skyhigh404/ESP32BiosignalMonitor/esp32/components/ad5941/include/ad5940.h

/**  
 * @file       ad5940.h
 * @brief      AD5940 library. This file contains all AD5940 library functions. 
 * @author     ADI
 * @date       March 2019
 * @par Revision History:
 * 
 * Copyright (c) 2017-2019 Analog Devices, Inc. All Rights Reserved.
 * 
 * This software is proprietary to Analog Devices, Inc. and its licensors.
 * By using this software you agree to the terms of the associated
 * Analog Devices Software License Agreement.
**/
#ifndef _AD5940_H_
#define _AD5940_H_
#include "math.h"
#include "string.h"
#include "stdio.h"
/** @addtogroup AD5940_Library
  * @{
  */

/** 
 * Select the correct chip.
 * Recommend to define this in your compiler.
 * */
//#define CHIPSEL_M355      /**< ADuCM355 */
//#define CHIPSEL_594X      /**< AD5940 or AD5941 */

/* library version number */
#define AD5940LIB_VER_MAJOR       0    /**< Major number */
#define AD5940LIB_VER_MINOR       2    /**< Minor number */
#define AD5940LIB_VER_PATCH       1    /**< Path number */
#define AD5940LIB_VER   (AD5940LIB_VER_MAJOR<<16)|(AD5940LIB_VER_MINOR<<8)|(AD5940LIB_VER_PATCH)

// #define ADI_DEBUG   /**< Comment this line to remove debug info. */

#ifdef ADI_DEBUG
#define ADI_Print printf   /**< Select the method to print out debug message */
#endif

#if defined(CHIPSEL_M355) && defined(CHIPSEL_594X)
#error Please select the correct chip by define CHIPSEL_M355 or CHIPSEL_594X.
#endif

#if !defined(CHIPSEL_M355) && !defined(CHIPSEL_594X)
#error Please select the correct chip by define CHIPSEL_M355 or CHIPSEL_594X.
#endif

/** 
 * @cond
 * @defgroup AD5940RegistersBitfields
 * @brief All AD5940 registers and bitfields definition.
 * @{
*/
//#if defined(_LANGUAGE_C) || (defined(__GNUC__) && !defined(__ASSEMBLER__))
#include <stdint.h>
//#endif /* _LANGUAGE_C */

#ifndef __ADI_GENERATED_DEF_HEADERS__
#define __ADI_GENERATED_DEF_HEADERS__    1
#endif

#define __ADI_HAS_AGPIO__          1
#define __ADI_HAS_ALLON__          1
#define __ADI_HAS_INTC__           1
#define __ADI_HAS_AFECON__         1
#define __ADI_HAS_WUPTMR__         1
#define __ADI_HAS_AFE__            1

/* ============================================================================================================================
        GPIO
   ============================================================================================================================ */

/* ============================================================================================================================
        AGPIO
   ============================================================================================================================ */
#define REG_AGPIO_GP0CON_RESET               0x00000000            /*      Reset Value for GP0CON  */
#define REG_AGPIO_GP0CON                     0x00000000            /*  AGPIO GPIO Port 0 Configuration */
#define REG_AGPIO_GP0OEN_RESET               0x00000000            /*      Reset Value for GP0OEN  */
#define REG_AGPIO_GP0OEN                     0x00000004            /*  AGPIO GPIO Port 0 Output Enable */
#define REG_AGPIO_GP0PE_RESET                0x00000000            /*      Reset Value for GP0PE  */
#define REG_AGPIO_GP0PE                      0x00000008            /*  AGPIO GPIO Port 0 Pullup/Pulldown Enable */
#define REG_AGPIO_GP0IEN_RESET               0x00000000            /*      Reset Value for GP0IEN  */
#define REG_AGPIO_GP0IEN                     0x0000000C            /*  AGPIO GPIO Port 0 Input Path Enable */
#define REG_AGPIO_GP0IN_RESET                0x00000000            /*      Reset Value for GP0IN  */
#define REG_AGPIO_GP0IN                      0x00000010            /*  AGPIO GPIO Port 0 Registered Data Input */
#define REG_AGPIO_GP0OUT_RESET               0x00000000            /*      Reset Value for GP0OUT  */
#define REG_AGPIO_GP0OUT                     0x00000014            /*  AGPIO GPIO Port 0 Data Output */
#define REG_AGPIO_GP0SET_RESET               0x00000000            /*      Reset Value for GP0SET  */
#define REG_AGPIO_GP0SET                     0x00000018            /*  AGPIO GPIO Port 0 Data Out Set */
#define REG_AGPIO_GP0CLR_RESET               0x00000000            /*      Reset Value for GP0CLR  */
#define REG_AGPIO_GP0CLR                     0x0000001C            /*  AGPIO GPIO Port 0 Data Out Clear */
#define REG_AGPIO_GP0TGL_RESET               0x00000000            /*      Reset Value for GP0TGL  */
#define REG_AGPIO_GP0TGL                     0x00000020            /*  AGPIO GPIO Port 0 Pin Toggle */

/* ============================================================================================================================
        AGPIO Register BitMasks, Positions & Enumerations 
   ============================================================================================================================ */
/* -------------------------------------------------------------------------------------------------------------------------
          AGPIO_GP0CON                         Pos/Masks         Description
   ------------------------------------------------------------------------------------------------------------------------- */
#define BITP_AGPIO_GP0CON_PIN7CFG            14            /*  P0.7 Configuration Bits */
#define BITP_AGPIO_GP0CON_PIN6CFG            12            /*  P0.6 Configuration Bits */
#define BITP_AGPIO_GP0CON_PIN5CFG            10            /*  P0.5 Configuration Bits */
#define BITP_AGPIO_GP0CON_PIN4CFG             8            /*  P0.4 Configuration Bits */
#define BITP_AGPIO_GP0CON_PIN3CFG             6            /*  P0.3 Configuration Bits */
#define BITP_AGPIO_GP0CON_PIN2CFG             4            /*  P0.2 Configuration Bits */
#define BITP_AGPIO_GP0CON_PIN1CFG             2            /*  P0.1 Configuration Bits */
#define BITP_AGPIO_GP0CON_PIN0CFG             0            /*  P0.0 Configuration Bits */
#define BITM_AGPIO_GP0CON_PIN7CFG            0x0000C000    /*  P0.7 Configuration Bits */
#define BITM_AGPIO_GP0CON_PIN6CFG            0x00003000    /*  P0.6 Configuration Bits */
#define BITM_AGPIO_GP0CON_PIN5CFG            0x00000C00    /*  P0.5 Configuration Bits */
#define BITM_AGPIO_GP0CON_PIN4CFG            0x00000300    /*  P0.4 Configuration Bits */
#define BITM_AGPIO_GP0CON_PIN3CFG            0x000000C0    /*  P0.3 Configuration Bits */
#define BITM_AGPIO_GP0CON_PIN2CFG            0x00000030    /*  P0.2 Configuration Bits */
#define BITM_AGPIO_GP0CON_PIN1CFG            0x0000000C    /*  P0.1 Configuration Bits */
#define BITM_AGPIO_GP0CON_PIN0CFG            0x00000003    /*  P0.0 Configuration Bits */

/* -------------------------------------------------------------------------------------------------------------------------
          AGPIO_GP0OEN                         Pos/Masks         Description
   ------------------------------------------------------------------------------------------------------------------------- */
#define BITP_AGPIO_GP0OEN_OEN                 0            /*  Pin Output Drive Enable */
#define BITM_AGPIO_GP0OEN_OEN                0x000000FF    /*  Pin Output Drive Enable */

/* -------------------------------------------------------------------------------------------------------------------------
          AGPIO_GP0PE                          Pos/Masks         Description
   ------------------------------------------------------------------------------------------------------------------------- */
#define BITP_AGPIO_GP0PE_PE                   0            /*  Pin Pull Enable */
#define BITM_AGPIO_GP0PE_PE                  0x000000FF    /*  Pin Pull Enable */

/* -------------------------------------------------------------------------------------------------------------------------
          AGPIO_GP0IEN                         Pos/Masks         Description
   ------------------------------------------------------------------------------------------------------------------------- */
#define BITP_AGPIO_GP0IEN_IEN                 0            /*  Input Path Enable */
#define BITM_AGPIO_GP0IEN_IEN                0x000000FF    /*  Input Path Enable */

/* -------------------------------------------------------------------------------------------------------------------------
          AGPIO_GP0IN                          Pos/Masks         Description
   ------------------------------------------------------------------------------------------------------------------------- */
#define BITP_AGPIO_GP0IN_IN                   0            /*  Registered Data Input */
#define BITM_AGPIO_GP0IN_IN                  0x000000FF    /*  Registered Data Input */

/* -------------------------------------------------------------------------------------------------------------------------
          AGPIO_GP0OUT                         Pos/Masks         Description
   ------------------------------------------------------------------------------------------------------------------------- */
#define BITP_AGPIO_GP0OUT_OUT                 0            /*  Data Out */
#define BITM_AGPIO_GP0OUT_OUT                0x000000FF    /*  Data Out */

/* -------------------------------------------------------------------------------------------------------------------------
          AGPIO_GP0SET                         Pos/Masks         Description
   ------------------------------------------------------------------------------------------------------------------------- */
#define BITP_AGPIO_GP0SET_SET                 0            /*  Set the Output HIGH */
#define BITM_AGPIO_GP0SET_SET                0x000000FF    /*  Set the Output HIGH */

/* -------------------------------------------------------------------------------------------------------------------------
          AGPIO_GP0CLR                         Pos/Masks         Description
   ------------------------------------------------------------------------------------------------------------------------- */
#define BITP_AGPIO_GP0CLR_CLR                 0            /*  Set the Output LOW */
#define BITM_AGPIO_GP0CLR_CLR                0x000000FF    /*  Set the Output LOW */

/* -------------------------------------------------------------------------------------------------------------------------
          AGPIO_GP0TGL                         Pos/Masks         Description
   ------------------------------------------------------------------------------------------------------------------------- */
#define BITP_AGPIO_GP0TGL_TGL                 0            /*  Toggle the Output */
#define BITM_AGPIO_GP0TGL_TGL                0x000000FF    /*  Toggle the Output */


/* ============================================================================================================================
        
   ============================================================================================================================ */

/* ============================================================================================================================
        AFECON
   ============================================================================================================================ */
#define REG_AFECON_ADIID_RESET               0x00000000            /*      Reset Value for ADIID  */
#define REG_AFECON_ADIID                     0x00000400            /*  AFECON ADI Identification */
#define REG_AFECON_CHIPID_RESET              0x00000000            /*      Reset Value for CHIPID  */
#define REG_AFECON_CHIPID                    0x00000404            /*  AFECON Chip Identification */
#define REG_AFECON_CLKCON0_RESET             0x00000441            /*      Reset Value for CLKCON0  */
#define REG_AFECON_CLKCON0                   0x00000408            /*  AFECON Clock Divider Configuration */
#define REG_AFECON_CLKEN1_RESET              0x000002C0            /*      Reset Value for CLKEN1  */
#define REG_AFECON_CLKEN1                    0x00000410            /*  AFECON Clock Gate Enable */
#define REG_AFECON_CLKSEL_RESET              0x00000000            /*      Reset Value for CLKSEL  */
#define REG_AFECON_CLKSEL                    0x00000414            /*  AFECON Clock Select */
#define REG_AFECON_CLKCON0KEY_RESET          0x00000000            /*      Reset Value for CLKCON0KEY  */
#define REG_AFECON_CLKCON0KEY                0x00000420            /*  AFECON Enable Clock Division to 8Mhz,4Mhz and 2Mhz */
#define REG_AFECON_SWRSTCON_RESET            0x00000001            /*      Reset Value for SWRSTCON  */
#define REG_AFECON_SWRSTCON                  0x00000424            /*  AFECON Software Reset */
#define REG_AFECON_TRIGSEQ_RESET             0x00000000            /*      Reset Value for TRIGSEQ  */
#define REG_AFECON_TRIGSEQ                   0x00000430            /*  AFECON Trigger Sequence */

/* ============================================================================================================================
        AFECON Register BitMasks, Positions & Enumerations 
   ============================================================================================================================ */
/* -------------------------------------------------------------------------------------------------------------------------
          AFECON_ADIID                         Pos/Masks         Description
   ------------------------------------------------------------------------------------------------------------------------- */
#define BITP_AFECON_ADIID_ADIID               0            /*  ADI Identifier. */
#define BITM_AFECON_ADIID_ADIID              0x0000FFFF    /*  ADI Identifier. */

/* -------------------------------------------------------------------------------------------------------------------------
          AFECON_CHIPID                        Pos/Masks         Description
   ------------------------------------------------------------------------------------------------------------------------- */
#define BITP_AFECON_CHIPID_PARTID             4            /*  Part Identifier */
#define BITP_AFECON_CHIPID_REVISION           0            /*  Silicon Revision Number */
#define BITM_AFECON_CHIPID_PARTID            0x0000FFF0    /*  Part Identifier */
#define BITM_AFECON_CHIPID_REVISION          0x0000000F    /*  Silicon Revision Number */

/* -------------------------------------------------------------------------------------------------------------------------
          AFECON_CLKCON0                       Pos/Masks         Description
   ------------------------------------------------------------------------------------------------------------------------- */
#define BITP_AFECON_CLKCON0_SFFTCLKDIVCNT    10            /*  SFFT Clock Divider Configuration */
#define BITP_AFECON_CLKCON0_ADCCLKDIV         6            /*  ADC Clock Divider Configuration */
#define BITP_AFECON_CLKCON0_SYSCLKDIV         0            /*  System Clock Divider Configuration */
#define BITM_AFECON_CLKCON0_SFFTCLKDIVCNT    0x0000FC00    /*  SFFT Clock Divider Configuration */
#define BITM_AFECON_CLKCON0_ADCCLKDIV        0x000003C0    /*  ADC Clock Divider Configuration */
#define BITM_AFECON_CLKCON0_SYSCLKDIV        0x0000003F    /*  System Clock Divider Configuration */

/* -------------------------------------------------------------------------------------------------------------------------
          AFECON_CLKEN1                        Pos/Masks         Description
   ------------------------------------------------------------------------------------------------------------------------- */
#define BITP_AFECON_CLKEN1_GPT1DIS            7            /*  GPT1 Clock Enable */
#define BITP_AFECON_CLKEN1_GPT0DIS            6            /*  GPT0 Clock Enable */
#define BITP_AFECON_CLKEN1_ACLKDIS            5            /*  ACLK Clock Enable */
#define BITM_AFECON_CLKEN1_GPT1DIS           0x00000080    /*  GPT1 Clock Enable */
#define BITM_AFECON_CLKEN1_GPT0DIS           0x00000040    /*  GPT0 Clock Enable */
#define BITM_AFECON_CLKEN1_ACLKDIS           0x00000020    /*  ACLK Clock Enable */

/* -------------------------------------------------------------------------------------------------------------------------
          AFECON_CLKSEL                        Pos/Masks         Description
   ------------------------------------------------------------------------------------------------------------------------- */
#define BITP_AFECON_CLKSEL_ADCCLKSEL          2            /*  Select ADC Clock Source */
#define BITP_AFECON_CLKSEL_SYSCLKSEL          0            /*  Select System Clock Source */
#define BITM_AFECON_CLKSEL_ADCCLKSEL         0x0000000C    /*  Select ADC Clock Source */
#define BITM_AFECON_CLKSEL_SYSCLKSEL         0x00000003    /*  Select System Clock Source */

/* -------------------------------------------------------------------------------------------------------------------------
          AFECON_CLKCON0KEY                    Pos/Masks         Description
   ------------------------------------------------------------------------------------------------------------------------- */
#define BITP_AFECON_CLKCON0KEY_DIVSYSCLK_ULP_EN  0            /*  Enable Clock Division to 8Mhz,4Mhz and 2Mhz */
#define BITM_AFECON_CLKCON0KEY_DIVSYSCLK_ULP_EN 0x0000FFFF    /*  Enable Clock Division to 8Mhz,4Mhz and 2Mhz */

/* -------------------------------------------------------------------------------------------------------------------------
          AFECON_SWRSTCON                      Pos/Masks         Description
   ------------------------------------------------------------------------------------------------------------------------- */
#define BITP_AFECON_SWRSTCON_SWRSTL           0            /*  Software Reset */
#define BITM_AFECON_SWRSTCON_SWRSTL          0x0000FFFF    /*  Software Reset */

/* -------------------------------------------------------------------------------------------------------------------------
          AFECON_TRIGSEQ                       Pos/Masks         Description
   ------------------------------------------------------------------------------------------------------------------------- */
#define BITP_AFECON_TRIGSEQ_TRIG3             3            /*  Trigger Sequence 3 */
#define BITP_AFECON_TRIGSEQ_TRIG2             2            /*  Trigger Sequence 2 */
#define BITP_AFECON_TRIGSEQ_TRIG1             1            /*  Trigger Sequence 1 */
#define BITP_AFECON_TRIGSEQ_TRIG0             0            /*  Trigger Sequence 0 */
#define BITM_AFECON_TRIGSEQ_TRIG3            0x00000008    /*  Trigger Sequence 3 */
#define BITM_AFECON_TRIGSEQ_TRIG2            0x00000004    /*  Trigger Sequence 2 */
#define BITM_AFECON_TRIGSEQ_TRIG1            0x00000002    /*  Trigger Sequence 1 */
#define BITM_AFECON_TRIGSEQ_TRIG0            0x00000001    /*  Trigger Sequence 0 */

/* ============================================================================================================================
        AFEWDT
   ============================================================================================================================ */
#define REG_AFEWDT_WDTLD                     0x00000900            /*  AFEWDT Watchdog Timer Load Value */
#define REG_AFEWDT_WDTVALS                   0x00000904            /*  AFEWDT Current Count Value */
#define REG_AFEWDT_WDTCON                    0x00000908            /*  AFEWDT Watchdog Timer Control Register */
#define REG_AFEWDT_WDTCLRI                   0x0000090C            /*  AFEWDT Refresh Watchdog Register */
#define REG_AFEWDT_WDTSTA                    0x00000918            /*  AFEWDT Timer Status */
#define REG_AFEWDT_WDTMINLD                  0x0000091C            /*  AFEWDT Minimum Load Value */

/* ============================================================================================================================
        AFEWDT Register BitMasks, Positions & Enumerations 
   ============================================================================================================================ */
/* -------------------------------------------------------------------------------------------------------------------------
          AFEWDT_WDTLD                         Pos/Masks         Description
   ------------------------------------------------------------------------------------------------------------------------- */
#define BITP_AFEWDT_WDTLD_LOAD                0            /*  WDT Load Value */
#define BITM_AFEWDT_WDTLD_LOAD               (_ADI_MSK_3(0x0000FFFF,0x0000FFFF, int16_t   ))    /*  WDT Load Value */

/* -------------------------------------------------------------------------------------------------------------------------
          AFEWDT_WDTVALS                       Pos/Masks         Description
   ------------------------------------------------------------------------------------------------------------------------- */
#define BITP_AFEWDT_WDTVALS_CCOUNT            0            /*  Current WDT Count Value. */
#define BITM_AFEWDT_WDTVALS_CCOUNT           (_ADI_MSK_3(0x0000FFFF,0x0000FFFF, int16_t   ))    /*  Current WDT Count Value. */

/* -------------------------------------------------------------------------------------------------------------------------
          AFEWDT_WDTCON                        Pos/Masks         Description
   ------------------------------------------------------------------------------------------------------------------------- */
#define BITP_AFEWDT_WDTCON_RESERVED_15_11    11            /*  RESERVED */
#define BITP_AFEWDT_WDTCON_WDTIRQEN          10            /*  WDT Interrupt Enable */
#define BITP_AFEWDT_WDTCON_MINLOAD_EN         9            /*  Timer Window Control */
#define BITP_AFEWDT_WDTCON_CLKDIV2            8            /*  Clock Source */
#define BITP_AFEWDT_WDTCON_RESERVED1_7        7            /*  Reserved */
#define BITP_AFEWDT_WDTCON_MDE                6            /*  Timer Mode Select */
#define BITP_AFEWDT_WDTCON_EN                 5            /*  Timer Enable */
#define BITP_AFEWDT_WDTCON_PRE                2            /*  Prescaler. */
#define BITP_AFEWDT_WDTCON_IRQ                1            /*  WDT Interrupt Enable */
#define BITP_AFEWDT_WDTCON_PDSTOP             0            /*  Power Down Stop Enable */
#define BITM_AFEWDT_WDTCON_RESERVED_15_11    (_ADI_MSK_3(0x0000F800,0x0000F800U, uint16_t  ))    /*  RESERVED */
#define BITM_AFEWDT_WDTCON_WDTIRQEN          (_ADI_MSK_3(0x00000400,0x00000400U, uint16_t  ))    /*  WDT Interrupt Enable */
#define BITM_AFEWDT_WDTCON_MINLOAD_EN        (_ADI_MSK_3(0x00000200,0x00000200U, uint16_t  ))    /*  Timer Window Control */
#define BITM_AFEWDT_WDTCON_CLKDIV2           (_ADI_MSK_3(0x00000100,0x00000100U, uint16_t  ))    /*  Clock Source */
#define BITM_AFEWDT_WDTCON_RESERVED1_7       (_ADI_MSK_3(0x00000080,0x00000080U, uint16_t  ))    /*  Reserved */
#define BITM_AFEWDT_WDTCON_MDE               (_ADI_MSK_3(0x00000040,0x00000040U, uint16_t  ))    /*  Timer Mode Select */
#define BITM_AFEWDT_WDTCON_EN                (_ADI_MSK_3(0x00000020,0x00000020U, uint16_t  ))    /*  Timer Enable */
#define BITM_AFEWDT_WDTCON_PRE               (_ADI_MSK_3(0x0000000C,0x0000000CU, uint16_t  ))    /*  Prescaler. */
#define BITM_AFEWDT_WDTCON_IRQ               (_ADI_MSK_3(0x00000002,0x00000002U, uint16_t  ))    /*  WDT Interrupt Enable */
#define BITM_AFEWDT_WDTCON_PDSTOP            (_ADI_MSK_3(0x00000001,0x00000001U, uint16_t  ))    /*  Power Down Stop Enable */
#define ENUM_AFEWDT_WDTCON_RESET             (_ADI_MSK_3(0x00000000,0x00000000U, uint16_t  ))    /*  IRQ: Watchdog Timer timeout creates a reset. */
#define ENUM_AFEWDT_WDTCON_INTERRUPT         (_ADI_MSK_3(0x00000002,0x00000002U, uint16_t  ))    /*  IRQ: Watchdog Timer  timeout creates an interrupt instead of reset. */
#define ENUM_AFEWDT_WDTCON_CONTINUE          (_ADI_MSK_3(0x00000000,0x00000000U, uint16_t  ))    /*  PDSTOP: Continue Counting When In Hibernate */
#define ENUM_AFEWDT_WDTCON_STOP              (_ADI_MSK_3(0x00000001,0x00000001U, uint16_t  ))    /*  PDSTOP: Stop Counter When In Hibernate. */

/* -------------------------------------------------------------------------------------------------------------------------
          AFEWDT_WDTCLRI                       Pos/Masks         Description
   ------------------------------------------------------------------------------------------------------------------------- */
#define BITP_AFEWDT_WDTCLRI_CLRWDG            0            /*  Refresh Register */
#define BITM_AFEWDT_WDTCLRI_CLRWDG           (_ADI_MSK_3(0x0000FFFF,0x0000FFFF, int16_t   ))    /*  Refresh Register */

/* -------------------------------------------------------------------------------------------------------------------------
          AFEWDT_WDTSTA                        Pos/Masks         Description
   ------------------------------------------------------------------------------------------------------------------------- */
#define BITP_AFEWDT_WDTSTA_RESERVED_15_7      7            /*  RESERVED */
#define BITP_AFEWDT_WDTSTA_TMINLD             6            /*  WDTMINLD Write Status */
#define BITP_AFEWDT_WDTSTA_OTPWRDONE          5            /*  Reset Type Status */
#define BITP_AFEWDT_WDTSTA_LOCK               4            /*  Lock Status */
#define BITP_AFEWDT_WDTSTA_CON                3            /*  WDTCON Write Status */
#define BITP_AFEWDT_WDTSTA_TLD                2            /*  WDTVAL Write Status */
#define BITP_AFEWDT_WDTSTA_CLRI               1            /*  WDTCLRI Write Status */
#define BITP_AFEWDT_WDTSTA_IRQ                0            /*  WDT Interrupt */
#define BITM_AFEWDT_WDTSTA_RESERVED_15_7     (_ADI_MSK_3(0x0000FF80,0x0000FF80U, uint16_t  ))    /*  RESERVED */
#define BITM_AFEWDT_WDTSTA_TMINLD            (_ADI_MSK_3(0x00000040,0x00000040U, uint16_t  ))    /*  WDTMINLD Write Status */
#define BITM_AFEWDT_WDTSTA_OTPWRDONE         (_ADI_MSK_3(0x00000020,0x00000020U, uint16_t  ))    /*  Reset Type Status */
#define BITM_AFEWDT_WDTSTA_LOCK              (_ADI_MSK_3(0x00000010,0x00000010U, uint16_t  ))    /*  Lock Status */
#define BITM_AFEWDT_WDTSTA_CON               (_ADI_MSK_3(0x00000008,0x00000008U, uint16_t  ))    /*  WDTCON Write Status */
#define BITM_AFEWDT_WDTSTA_TLD               (_ADI_MSK_3(0x00000004,0x00000004U, uint16_t  ))    /*  WDTVAL Write Status */
#define BITM_AFEWDT_WDTSTA_CLRI              (_ADI_MSK_3(0x00000002,0x00000002U, uint16_t  ))    /*  WDTCLRI Write Status */
#define BITM_AFEWDT_WDTSTA_IRQ               (_ADI_MSK_3(0x00000001,0x00000001U, uint16_t  ))    /*  WDT Interrupt */
#define ENUM_AFEWDT_WDTSTA_OPEN              (_ADI_MSK_3(0x00000000,0x00000000U, uint16_t  ))    /*  LOCK: Timer Operation Not Locked */
#define ENUM_AFEWDT_WDTSTA_LOCKED            (_ADI_MSK_3(0x00000010,0x00000010U, uint16_t  ))    /*  LOCK: Timer Enabled and Locked */
#define ENUM_AFEWDT_WDTSTA_SYNC_COMPLETE     (_ADI_MSK_3(0x00000000,0x00000000U, uint16_t  ))    /*  TLD: Arm and AFE Watchdog Clock Domains WDTLD values match */
#define ENUM_AFEWDT_WDTSTA_SYNC_IN_PROGRESS  (_ADI_MSK_3(0x00000004,0x00000004U, uint16_t  ))    /*  TLD: Synchronize In Progress */
#define ENUM_AFEWDT_WDTSTA_CLEARED           (_ADI_MSK_3(0x00000000,0x00000000U, uint16_t  ))    /*  IRQ: Watchdog Timer Interrupt Not Pending */
#define ENUM_AFEWDT_WDTSTA_PENDING           (_ADI_MSK_3(0x00000001,0x00000001U, uint16_t  ))    /*  IRQ: Watchdog Timer Interrupt Pending */

/* -------------------------------------------------------------------------------------------------------------------------
          AFEWDT_WDTMINLD                      Pos/Masks         Description
   ------------------------------------------------------------------------------------------------------------------------- */
#define BITP_AFEWDT_WDTMINLD_MIN_LOAD         0            /*  WDT Min Load Value */
#define BITM_AFEWDT_WDTMINLD_MIN_LOAD        (_ADI_MSK_3(0x0000FFFF,0x0000FFFF, int16_t   ))    /*  WDT Min Load Value */

/* ============================================================================================================================
        Wakeup Timer
   ============================================================================================================================ */

/* ============================================================================================================================
        WUPTMR
   ============================================================================================================================ */
#define REG_WUPTMR_CON_RESET                 0x00000000            /*      Reset Value for CON  */
#define REG_WUPTMR_CON                       0x00000800            /*  WUPTMR Timer Control */
#define REG_WUPTMR_SEQORDER_RESET            0x00000000            /*      Reset Value for SEQORDER  */
#define REG_WUPTMR_SEQORDER                  0x00000804            /*  WUPTMR Order Control */
#define REG_WUPTMR_SEQ0WUPL_RESET            0x0000FFFF            /*      Reset Value for SEQ0WUPL  */
#define REG_WUPTMR_SEQ0WUPL                  0x00000808            /*  WUPTMR SEQ0 WTimeL (LSB) */
#define REG_WUPTMR_SEQ0WUPH_RESET            0x0000000F            /*      Reset Value for SEQ0WUPH  */
#define REG_WUPTMR_SEQ0WUPH                  0x0000080C            /*  WUPTMR SEQ0 WTimeH (MSB) */
#define REG_WUPTMR_SEQ0SLEEPL_RESET          0x0000FFFF            /*      Reset Value for SEQ0SLEEPL  */
#define REG_WUPTMR_SEQ0SLEEPL                0x00000810            /*  WUPTMR SEQ0 STimeL (LSB) */
#define REG_WUPTMR_SEQ0SLEEPH_RESET          0x0000000F            /*      Reset Value for SEQ0SLEEPH  */
#define REG_WUPTMR_SEQ0SLEEPH                0x00000814            /*  WUPTMR SEQ0 STimeH (MSB) */
#define REG_WUPTMR_SEQ1WUPL_RESET            0x0000FFFF            /*      Reset Value for SEQ1WUPL  */
#define REG_WUPTMR_SEQ1WUPL                  0x00000818            /*  WUPTMR SEQ1 WTimeL (LSB) */
#define REG_WUPTMR_SEQ1WUPH_RESET            0x0000000F            /*      Reset Value for SEQ1WUPH  */
#define REG_WUPTMR_SEQ1WUPH                  0x0000081C            /*  WUPTMR SEQ1 WTimeH (MSB) */
#define REG_WUPTMR_SEQ1SLEEPL_RESET          0x0000FFFF            /*      Reset Value for SEQ1SLEEPL  */
#define REG_WUPTMR_SEQ1SLEEPL                0x00000820            /*  WUPTMR SEQ1 STimeL (LSB) */
#define REG_WUPTMR_SEQ1SLEEPH_RESET          0x0000000F            /*      Reset Value for SEQ1SLEEPH  */
#define REG_WUPTMR_SEQ1SLEEPH                0x00000824            /*  WUPTMR SEQ1 STimeH (MSB) */
#define REG_WUPTMR_SEQ2WUPL_RESET            0x0000FFFF            /*      Reset Value for SEQ2WUPL  */
#define REG_WUPTMR_SEQ2WUPL                  0x00000828            /*  WUPTMR SEQ2 WTimeL (LSB) */
#define REG_WUPTMR_SEQ2WUPH_RESET            0x0000000F            /*      Reset Value for SEQ2WUPH  */
#define REG_WUPTMR_SEQ2WUPH                  0x0000082C            /*  WUPTMR SEQ2 WTimeH (MSB) */
#define REG_WUPTMR_SEQ2SLEEPL_RESET          0x0000FFFF            /*      Reset Value for SEQ2SLEEPL  */
#define REG_WUPTMR_SEQ2SLEEPL                0x00000830            /*  WUPTMR SEQ2 STimeL (LSB) */
#define REG_WUPTMR_SEQ2SLEEPH_RESET          0x0000000F            /*      Reset Value for SEQ2SLEEPH  */
#define REG_WUPTMR_SEQ2SLEEPH                0x00000834            /*  WUPTMR SEQ2 STimeH (MSB) */
#define REG_WUPTMR_SEQ3WUPL_RESET            0x0000FFFF            /*      Reset Value for SEQ3WUPL  */
#define REG_WUPTMR_SEQ3WUPL                  0x00000838            /*  WUPTMR SEQ3 WTimeL (LSB) */
#define REG_WUPTMR_SEQ3WUPH_RESET            0x0000000F            /*      Reset Value for SEQ3WUPH  */
#define REG_WUPTMR_SEQ3WUPH                  0x0000083C            /*  WUPTMR SEQ3 WTimeH (MSB) */
#define REG_WUPTMR_SEQ3SLEEPL_RESET          0x0000FFFF            /*      Reset Value for SEQ3SLEEPL  */
#define REG_WUPTMR_SEQ3SLEEPL                0x00000840            /*  WUPTMR SEQ3 STimeL (LSB) */
#define REG_WUPTMR_SEQ3SLEEPH_RESET          0x0000000F            /*      Reset Value for SEQ3SLEEPH  */
#define REG_WUPTMR_SEQ3SLEEPH                0x00000844            /*  WUPTMR SEQ3 STimeH (MSB) */

/* ============================================================================================================================
        WUPTMR Register BitMasks, Positions & Enumerations 
   ============================================================================================================================ */
/* -------------------------------------------------------------------------------------------------------------------------
          WUPTMR_CON                           Pos/Masks         Description
   ------------------------------------------------------------------------------------------------------------------------- */
#define BITP_WUPTMR_CON_MSKTRG                6            /*  Mark Sequence Trigger from Sleep Wakeup Timer */
#define BITP_WUPTMR_CON_CLKSEL                4            /*  Clock Selection */
#define BITP_WUPTMR_CON_ENDSEQ                1            /*  End Sequence */
#define BITP_WUPTMR_CON_EN                    0            /*  Sleep Wake Timer Enable Bit */
#define BITM_WUPTMR_CON_MSKTRG               0x00000040    /*  Mark Sequence Trigger from Sleep Wakeup Timer */
#define BITM_WUPTMR_CON_CLKSEL               0x00000030    /*  Clock Selection */
#define BITM_WUPTMR_CON_ENDSEQ               0x0000000E    /*  End Sequence */
#define BITM_WUPTMR_CON_EN                   0x00000001    /*  Sleep Wake Timer Enable Bit */
#define ENUM_WUPTMR_CON_SWT32K0              0x00000000            /*  CLKSEL: Internal 32kHz OSC */
#define ENUM_WUPTMR_CON_SWTEXT0              0x00000010            /*  CLKSEL: External Clock */
#define ENUM_WUPTMR_CON_SWT32K               0x00000020            /*  CLKSEL: Internal 32kHz OSC */
#define ENUM_WUPTMR_CON_SWTEXT               0x00000030            /*  CLKSEL: External Clock */
#define ENUM_WUPTMR_CON_ENDSEQA              0x00000000            /*  ENDSEQ: The Sleep Wakeup Timer Will Stop At SeqA And Then Go Back To SeqA */
#define ENUM_WUPTMR_CON_ENDSEQB              0x00000002            /*  ENDSEQ: The Sleep Wakeup Timer Will Stop At SeqB And Then Go Back To SeqA */
#define ENUM_WUPTMR_CON_ENDSEQC              0x00000004            /*  ENDSEQ: The Sleep Wakeup Timer Will Stop At SeqC And Then Go Back To SeqA */
#define ENUM_WUPTMR_CON_ENDSEQD              0x00000006            /*  ENDSEQ: The Sleep Wakeup Timer Will Stop At SeqD And Then Go Back To SeqA */
#define ENUM_WUPTMR_CON_ENDSEQE              0x00000008            /*  ENDSEQ: The Sleep Wakeup Timer Will Stop At SeqE And Then Go Back To SeqA */
#define ENUM_WUPTMR_CON_ENDSEQF              0x0000000A            /*  ENDSEQ: The Sleep Wakeup Timer Will Stop At SeqF And Then Go Back To SeqA */
#define ENUM_WUPTMR_CON_ENDSEQG              0x0000000C            /*  ENDSEQ: The Sleep Wakeup Timer Will Stop At SeqG And Then Go Back To SeqA */
#define ENUM_WUPTMR_CON_ENDSEQH              0x0000000E            /*  ENDSEQ: The Sleep Wakeup Timer Will Stop At SeqH And Then Go Back To SeqA */
#define ENUM_WUPTMR_CON_SWTEN                0x00000000            /*  EN: Enable Sleep Wakeup Timer */
#define ENUM_WUPTMR_CON_SWTDIS               0x00000001            /*  EN: Disable Sleep Wakeup Timer */

/* -------------------------------------------------------------------------------------------------------------------------
          WUPTMR_SEQORDER                      Pos/Masks         Description
   ------------------------------------------------------------------------------------------------------------------------- */
#define BITP_WUPTMR_SEQORDER_SEQH            14            /*  SEQH Config */
#define BITP_WUPTMR_SEQORDER_SEQG            12            /*  SEQG Config */
#define BITP_WUPTMR_SEQORDER_SEQF            10            /*  SEQF Config */
#define BITP_WUPTMR_SEQORDER_SEQE             8            /*  SEQE Config */
#define BITP_WUPTMR_SEQORDER_SEQD             6            /*  SEQD Config */
#define BITP_WUPTMR_SEQORDER_SEQC             4            /*  SEQC Config */
#define BITP_WUPTMR_SEQORDER_SEQB             2            /*  SEQB Config */
#define BITP_WUPTMR_SEQORDER_SEQA             0            /*  SEQA Config */
#define BITM_WUPTMR_SEQORDER_SEQH            0x0000C000    /*  SEQH Config */
#define BITM_WUPTMR_SEQORDER_SEQG            0x00003000    /*  SEQG Config */
#define BITM_WUPTMR_SEQORDER_SEQF            0x00000C00    /*  SEQF Config */
#define BITM_WUPTMR_SEQORDER_SEQE            0x00000300    /*  SEQE Config */
#define BITM_WUPTMR_SEQORDER_SEQD            0x000000C0    /*  SEQD Config */
#define BITM_WUPTMR_SEQORDER_SEQC            0x00000030    /*  SEQC Config */
#define BITM_WUPTMR_SEQORDER_SEQB            0x0000000C    /*  SEQB Config */
#define BITM_WUPTMR_SEQORDER_SEQA            0x00000003    /*  SEQA Config */
#define ENUM_WUPTMR_SEQORDER_SEQH0           0x00000000            /*  SEQH: Fill SEQ0 In */
#define ENUM_WUPTMR_SEQORDER_SEQH1           0x00004000            /*  SEQH: Fill SEQ1 In */
#define ENUM_WUPTMR_SEQORDER_SEQH2           0x00008000            /*  SEQH: Fill SEQ2 In */
#define ENUM_WUPTMR_SEQORDER_SEQH3           0x0000C000            /*  SEQH: Fill SEQ3 In */
#define ENUM_WUPTMR_SEQORDER_SEQG0           0x00000000            /*  SEQG: Fill SEQ0 In */
#define ENUM_WUPTMR_SEQORDER_SEQG1           0x00001000            /*  SEQG: Fill SEQ1 In */
#define ENUM_WUPTMR_SEQORDER_SEQG2           0x00002000            /*  SEQG: Fill SEQ2 In */
#define ENUM_WUPTMR_SEQORDER_SEQG3           0x00003000            /*  SEQG: Fill SEQ3 In */
#define ENUM_WUPTMR_SEQORDER_SEQF0           0x00000000            /*  SEQF: Fill SEQ0 In */
#define ENUM_WUPTMR_SEQORDER_SEQF1           0x00000400            /*  SEQF: Fill SEQ1 In */
#define ENUM_WUPTMR_SEQORDER_SEQF2           0x00000800            /*  SEQF: Fill SEQ2 In */
#define ENUM_WUPTMR_SEQORDER_SEQF3           0x00000C00            /*  SEQF: Fill SEQ3 In */
#define ENUM_WUPTMR_SEQORDER_SEQE0           0x00000000            /*  SEQE: Fill SEQ0 In */
#define ENUM_WUPTMR_SEQORDER_SEQE1           0x00000100            /*  SEQE: Fill SEQ1 In */
#define ENUM_WUPTMR_SEQORDER_SEQE2           0x00000200            /*  SEQE: Fill SEQ2 In */
#define ENUM_WUPTMR_SEQORDER_SEQE3           0x00000300            /*  SEQE: Fill SEQ3 In */
#define ENUM_WUPTMR_SEQORDER_SEQD0           0x00000000            /*  SEQD: Fill SEQ0 In */
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
#define BITP_WUPTMR_SEQ3SLEEPL_SLEEPTIME3     0            /*  Sequence 3 Active Period */
#define BITM_WUPTMR_SEQ3SLEEPL_SLEEPTIME3    0x0000FFFF    /*  Sequence 3 Active Period */

/* -------------------------------------------------------------------------------------------------------------------------
          WUPTMR_SEQ3SLEEPH                    Pos/Masks         Description
   ------------------------------------------------------------------------------------------------------------------------- */
#define BITP_WUPTMR_SEQ3SLEEPH_SLEEPTIME3     0            /*  Sequence 3 Active Period */
#define BITM_WUPTMR_SEQ3SLEEPH_SLEEPTIME3    0x0000000F    /*  Sequence 3 Active Period */


/* ============================================================================================================================
        Always On Register
   ============================================================================================================================ */

/* ============================================================================================================================
        ALLON
   ============================================================================================================================ */
#define REG_ALLON_PWRMOD_RESET               0x00000001            /*      Reset Value for PWRMOD  */
#define REG_ALLON_PWRMOD                     0x00000A00            /*  ALLON Power Modes */
#define REG_ALLON_PWRKEY_RESET               0x00000000            /*      Reset Value for PWRKEY  */
#define REG_ALLON_PWRKEY                     0x00000A04            /*  ALLON Key Protection for PWRMOD */
#define REG_ALLON_OSCKEY_RESET               0x00000000            /*      Reset Value for OSCKEY  */
#define REG_ALLON_OSCKEY                     0x00000A0C            /*  ALLON Key Protection for OSCCON */
#define REG_ALLON_OSCCON_RESET               0x00000003            /*      Reset Value for OSCCON  */
#define REG_ALLON_OSCCON                     0x00000A10            /*  ALLON Oscillator Control */
#define REG_ALLON_TMRCON_RESET               0x00000000            /*      Reset Value for TMRCON  */
#define REG_ALLON_TMRCON                     0x00000A1C            /*  ALLON Timer Wakeup Configuration */
#define REG_ALLON_EI0CON_RESET               0x00000000            /*      Reset Value for EI0CON  */
#define REG_ALLON_EI0CON                     0x00000A20            /*  ALLON External Interrupt Configuration 0 */
#define REG_ALLON_EI1CON_RESET               0x00000000            /*      Reset Value for EI1CON  */
#define REG_ALLON_EI1CON                     0x00000A24            /*  ALLON External Interrupt Configuration 1 */
#define REG_ALLON_EI2CON_RESET               0x00000000            /*      Reset Value for EI2CON  */
#define REG_ALLON_EI2CON                     0x00000A28            /*  ALLON External Interrupt Configuration 2 */
#define REG_ALLON_EICLR_RESET                0x0000C000            /*      Reset Value for EICLR  */
#define REG_ALLON_EICLR                      0x00000A30            /*  ALLON External Interrupt Clear */
#define REG_ALLON_RSTSTA_RESET               0x00000000            /*      Reset Value for RSTSTA  */
#define REG_ALLON_RSTSTA                     0x00000A40            /*  ALLON Reset Status */
#define REG_ALLON_RSTCONKEY_RESET            0x00000000            /*      Reset Value for RSTCONKEY  */
#define REG_ALLON_RSTCONKEY                  0x00000A5C            /*  ALLON Key Protection for RSTCON Register */
#define REG_ALLON_LOSCTST_RESET              0x0000008F            /*      Reset Value for LOSCTST  */
#define REG_ALLON_LOSCTST                    0x00000A6C            /*  ALLON Internal LF Oscillator Test */
#define REG_ALLON_CLKEN0_RESET               0x00000004            /*      Reset Value for CLKEN0  */
#define REG_ALLON_CLKEN0                     0x00000A70            /*  ALLON 32KHz Peripheral Clock Enable */

/* ============================================================================================================================
        ALLON Register BitMasks, Positions & Enumerations 
   ============================================================================================================================ */
/* -------------------------------------------------------------------------------------------------------------------------
          ALLON_PWRMOD                         Pos/Masks         Description
   ------------------------------------------------------------------------------------------------------------------------- */
#define BITP_ALLON_PWRMOD_RAMRETEN           15            /*  Retention for RAM */
#define BITP_ALLON_PWRMOD_ADCRETEN           14            /*  Keep ADC Power Switch on in Hibernate */
#define BITP_ALLON_PWRMOD_SEQSLPEN            3            /*  Auto Sleep by Sequencer Command */
#define BITP_ALLON_PWRMOD_TMRSLPEN            2            /*  Auto Sleep by Sleep Wakeup Timer */
#define BITP_ALLON_PWRMOD_PWRMOD              0            /*  Power Mode Control Bits */
#define BITM_ALLON_PWRMOD_RAMRETEN           0x00008000    /*  Retention for RAM */
#define BITM_ALLON_PWRMOD_ADCRETEN           0x00004000    /*  Keep ADC Power Switch on in Hibernate */
#define BITM_ALLON_PWRMOD_SEQSLPEN           0x00000008    /*  Auto Sleep by Sequencer Command */
#define BITM_ALLON_PWRMOD_TMRSLPEN           0x00000004    /*  Auto Sleep by Sleep Wakeup Timer */
#define BITM_ALLON_PWRMOD_PWRMOD             0x00000003    /*  Power Mode Control Bits */

/* -------------------------------------------------------------------------------------------------------------------------
          ALLON_PWRKEY                         Pos/Masks         Description
   ------------------------------------------------------------------------------------------------------------------------- */
#define BITP_ALLON_PWRKEY_PWRKEY              0            /*  PWRMOD Key Register */
#define BITM_ALLON_PWRKEY_PWRKEY             0x0000FFFF    /*  PWRMOD Key Register */

/* -------------------------------------------------------------------------------------------------------------------------
          ALLON_OSCKEY                         Pos/Masks         Description
   ------------------------------------------------------------------------------------------------------------------------- */
#define BITP_ALLON_OSCKEY_OSCKEY              0            /*  Oscillator Control Key Register. */
#define BITM_ALLON_OSCKEY_OSCKEY             0x0000FFFF    /*  Oscillator Control Key Register. */

/* -------------------------------------------------------------------------------------------------------------------------
          ALLON_OSCCON                         Pos/Masks         Description
   ------------------------------------------------------------------------------------------------------------------------- */
#define BITP_ALLON_OSCCON_HFXTALOK           10            /*  Status of HFXTAL Oscillator */
#define BITP_ALLON_OSCCON_HFOSCOK             9            /*  Status of HFOSC Oscillator */
#define BITP_ALLON_OSCCON_LFOSCOK             8            /*  Status of LFOSC Oscillator */
#define BITP_ALLON_OSCCON_HFXTALEN            2            /*  High Frequency Crystal Oscillator Enable */
#define BITP_ALLON_OSCCON_HFOSCEN             1            /*  High Frequency Internal Oscillator Enable */
#define BITP_ALLON_OSCCON_LFOSCEN             0            /*  Low Frequency Internal Oscillator Enable */
#define BITM_ALLON_OSCCON_HFXTALOK           0x00000400    /*  Status of HFXTAL Oscillator */
#define BITM_ALLON_OSCCON_HFOSCOK            0x00000200    /*  Status of HFOSC Oscillator */
#define BITM_ALLON_OSCCON_LFOSCOK            0x00000100    /*  Status of LFOSC Oscillator */
#define BITM_ALLON_OSCCON_HFXTALEN           0x00000004    /*  High Frequency Crystal Oscillator Enable */
#define BITM_ALLON_OSCCON_HFOSCEN            0x00000002    /*  High Frequency Internal Oscillator Enable */
#define BITM_ALLON_OSCCON_LFOSCEN            0x00000001    /*  Low Frequency Internal Oscillator Enable */

/* -------------------------------------------------------------------------------------------------------------------------
          ALLON_TMRCON                         Pos/Masks         Description
   ------------------------------------------------------------------------------------------------------------------------- */
#define BITP_ALLON_TMRCON_TMRINTEN            0            /*  Enable Wakeup Timer */
#define BITM_ALLON_TMRCON_TMRINTEN           0x00000001    /*  Enable Wakeup Timer */

/* -------------------------------------------------------------------------------------------------------------------------
          ALLON_EI0CON                         Pos/Masks         Description
   ------------------------------------------------------------------------------------------------------------------------- */
#define BITP_ALLON_EI0CON_IRQ3EN             15            /*  External Interrupt 3 Enable Bit */
#define BITP_ALLON_EI0CON_IRQ3MDE            12            /*  External Interrupt 3 Mode Registers */
#define BITP_ALLON_EI0CON_IRQ2EN             11            /*  External Interrupt 2 Enable Bit */
#define BITP_ALLON_EI0CON_IRQ2MDE             8            /*  External Interrupt 2 Mode Registers */
#define BITP_ALLON_EI0CON_IRQ1EN              7            /*  External Interrupt 1 Enable Bit */
#define BITP_ALLON_EI0CON_IRQ1MDE             4            /*  External Interrupt 1 Mode Registers */
#define BITP_ALLON_EI0CON_IRQ0EN              3            /*  External Interrupt 0 Enable Bit */
#define BITP_ALLON_EI0CON_IRQ0MDE             0            /*  External Interrupt 0 Mode Registers */
#define BITM_ALLON_EI0CON_IRQ3EN             0x00008000    /*  External Interrupt 3 Enable Bit */
#define BITM_ALLON_EI0CON_IRQ3MDE            0x00007000    /*  External Interrupt 3 Mode Registers */
#define BITM_ALLON_EI0CON_IRQ2EN             0x00000800    /*  External Interrupt 2 Enable Bit */
#define BITM_ALLON_EI0CON_IRQ2MDE            0x00000700    /*  External Interrupt 2 Mode Registers */
#define BITM_ALLON_EI0CON_IRQ1EN             0x00000080    /*  External Interrupt 1 Enable Bit */
#define BITM_ALLON_EI0CON_IRQ1MDE            0x00000070    /*  External Interrupt 1 Mode Registers */
#define BITM_ALLON_EI0CON_IRQ0EN             0x00000008    /*  External Interrupt 0 Enable Bit */
#define BITM_ALLON_EI0CON_IRQ0MDE            0x00000007    /*  External Interrupt 0 Mode Registers */

/* -------------------------------------------------------------------------------------------------------------------------
          ALLON_EI1CON                         Pos/Masks         Description
   ------------------------------------------------------------------------------------------------------------------------- */
#define BITP_ALLON_EI1CON_IRQ7EN             15            /*  External Interrupt 7 Enable Bit */
#define BITP_ALLON_EI1CON_IRQ7MDE            12            /*  External Interrupt 7 Mode Registers */
#define BITP_ALLON_EI1CON_IRQ6EN             11            /*  External Interrupt 6 Enable Bit */
#define BITP_ALLON_EI1CON_IRQ6MDE             8            /*  External Interrupt 6 Mode Registers */
#define BITP_ALLON_EI1CON_IRQ5EN              7            /*  External Interrupt 5 Enable Bit */
#define BITP_ALLON_EI1CON_IRQ5MDE             4            /*  External Interrupt 5 Mode Registers */
#define BITP_ALLON_EI1CON_IRQ4EN              3            /*  External Interrupt 4 Enable Bit */
#define BITP_ALLON_EI1CON_IRQ4MDE             0            /*  External Interrupt 4 Mode Registers */
#define BITM_ALLON_EI1CON_IRQ7EN             0x00008000    /*  External Interrupt 7 Enable Bit */
#define BITM_ALLON_EI1CON_IRQ7MDE            0x00007000    /*  External Interrupt 7 Mode Registers */
#define BITM_ALLON_EI1CON_IRQ6EN             0x00000800    /*  External Interrupt 6 Enable Bit */
#define BITM_ALLON_EI1CON_IRQ6MDE            0x00000700    /*  External Interrupt 6 Mode Registers */
#define BITM_ALLON_EI1CON_IRQ5EN             0x00000080    /*  External Interrupt 5 Enable Bit */
#define BITM_ALLON_EI1CON_IRQ5MDE            0x00000070    /*  External Interrupt 5 Mode Registers */
#define BITM_ALLON_EI1CON_IRQ4EN             0x00000008    /*  External Interrupt 4 Enable Bit */
#define BITM_ALLON_EI1CON_IRQ4MDE            0x00000007    /*  External Interrupt 4 Mode Registers */

/* -------------------------------------------------------------------------------------------------------------------------
          ALLON_EI2CON                         Pos/Masks         Description
   ------------------------------------------------------------------------------------------------------------------------- */
#define BITP_ALLON_EI2CON_BUSINTEN            3            /*  BUS Interrupt Detection Enable Bit */
#define BITP_ALLON_EI2CON_BUSINTMDE           0            /*  BUS Interrupt Detection Mode Registers */
#define BITM_ALLON_EI2CON_BUSINTEN           0x00000008    /*  BUS Interrupt Detection Enable Bit */
#define BITM_ALLON_EI2CON_BUSINTMDE          0x00000007    /*  BUS Interrupt Detection Mode Registers */

/* -------------------------------------------------------------------------------------------------------------------------
          ALLON_EICLR                          Pos/Masks         Description
   ------------------------------------------------------------------------------------------------------------------------- */
#define BITP_ALLON_EICLR_AUTCLRBUSEN         15            /*  Enable Auto Clear of Bus Interrupt */
#define BITP_ALLON_EICLR_BUSINT               8            /*  BUS Interrupt */
#define BITM_ALLON_EICLR_AUTCLRBUSEN         0x00008000    /*  Enable Auto Clear of Bus Interrupt */
#define BITM_ALLON_EICLR_BUSINT              0x00000100    /*  BUS Interrupt */

/* -------------------------------------------------------------------------------------------------------------------------
          ALLON_RSTSTA                         Pos/Masks         Description
   ------------------------------------------------------------------------------------------------------------------------- */
#define BITP_ALLON_RSTSTA_PINSWRST            4            /*  Software Reset Pin */
#define BITP_ALLON_RSTSTA_MMRSWRST            3            /*  MMR Software Reset */
#define BITP_ALLON_RSTSTA_WDRST               2            /*  Watchdog Timeout */
#define BITP_ALLON_RSTSTA_EXTRST              1            /*  External Reset */
#define BITP_ALLON_RSTSTA_POR                 0            /*  Power-on Reset */
#define BITM_ALLON_RSTSTA_PINSWRST           0x00000010    /*  Software Reset Pin */
#define BITM_ALLON_RSTSTA_MMRSWRST           0x00000008    /*  MMR Software Reset */
#define BITM_ALLON_RSTSTA_WDRST              0x00000004    /*  Watchdog Timeout */
#define BITM_ALLON_RSTSTA_EXTRST             0x00000002    /*  External Reset */
#define BITM_ALLON_RSTSTA_POR                0x00000001    /*  Power-on Reset */

/* -------------------------------------------------------------------------------------------------------------------------
          ALLON_RSTCONKEY                      Pos/Masks         Description
   ------------------------------------------------------------------------------------------------------------------------- */
#define BITP_ALLON_RSTCONKEY_KEY              0            /*  Reset Control Key Register */
#define BITM_ALLON_RSTCONKEY_KEY             0x0000FFFF    /*  Reset Control Key Register */

/* -------------------------------------------------------------------------------------------------------------------------
          ALLON_LOSCTST                        Pos/Masks         Description
   ------------------------------------------------------------------------------------------------------------------------- */
#define BITP_ALLON_LOSCTST_TRIM               0            /*  Trim Caps to Adjust Frequency. */
#define BITM_ALLON_LOSCTST_TRIM              0x0000000F    /*  Trim Caps to Adjust Frequency. */

/* -------------------------------------------------------------------------------------------------------------------------
          ALLON_CLKEN0                         Pos/Masks         Description
   ------------------------------------------------------------------------------------------------------------------------- */
#define BITP_ALLON_CLKEN0_TIACHPDIS           2            /*  TIA Chop Clock Disable */
#define BITP_ALLON_CLKEN0_SLPWUTDIS           1            /*  Sleep/Wakeup Timer Clock Disable */
#define BITP_ALLON_CLKEN0_WDTDIS              0            /*  Watch Dog Timer Clock Disable */
#define BITM_ALLON_CLKEN0_TIACHPDIS          0x00000004    /*  TIA Chop Clock Disable */
#define BITM_ALLON_CLKEN0_SLPWUTDIS          0x00000002    /*  Sleep/Wakeup Timer Clock Disable */
#define BITM_ALLON_CLKEN0_WDTDIS             0x00000001    /*  Watch Dog Timer Clock Disable */

/* ============================================================================================================================
        General Purpose Timer
   ============================================================================================================================ */

/* ============================================================================================================================
        AGPT0
   ============================================================================================================================ */
#define REG_AGPT0_LD0                        0x00000D00            /*  AGPT0 16-bit Load Value Register. */
#define REG_AGPT0_VAL0                       0x00000D04            /*  AGPT0 16-Bit Timer Value Register. */
#define REG_AGPT0_CON0                       0x00000D08            /*  AGPT0 Control Register. */
#define REG_AGPT0_CLRI0                      0x00000D0C            /*  AGPT0 Clear Interrupt Register. */
#define REG_AGPT0_CAP0                       0x00000D10            /*  AGPT0 Capture Register. */
#define REG_AGPT0_ALD0                       0x00000D14            /*  AGPT0 16-Bit Load Value, Asynchronous. */
#define REG_AGPT0_AVAL0                      0x00000D18            /*  AGPT0 16-Bit Timer Value, Asynchronous Register. */
#define REG_AGPT0_STA0                       0x00000D1C            /*  AGPT0 Status Register. */
#define REG_AGPT0_PWMCON0                    0x00000D20            /*  AGPT0 PWM Control Register. */
#define REG_AGPT0_PWMMAT0                    0x00000D24            /*  AGPT0 PWM Match Value Register. */
#define REG_AGPT0_INTEN                      0x00000D28            /*  AGPT0 Interrupt Enable */

/* ============================================================================================================================
        AGPT0 Register BitMasks, Positions & Enumerations 
   ============================================================================================================================ */
/* -------------------------------------------------------------------------------------------------------------------------
          AGPT0_LD0                            Pos/Masks         Description
   ------------------------------------------------------------------------------------------------------------------------- */
#define BITP_AGPT0_LD0_LOAD                   0            /*  Load Value */
#define BITM_AGPT0_LD0_LOAD                  (_ADI_MSK_3(0x0000FFFF,0x0000FFFF, int16_t   ))    /*  Load Value */

/* -------------------------------------------------------------------------------------------------------------------------
          AGPT0_VAL0                           Pos/Masks         Description
   ------------------------------------------------------------------------------------------------------------------------- */
#define BITP_AGPT0_VAL0_VAL                   0            /*  Current Count */
#define BITM_AGPT0_VAL0_VAL                  (_ADI_MSK_3(0x0000FFFF,0x0000FFFF, int16_t   ))    /*  Current Count */

/* -------------------------------------------------------------------------------------------------------------------------
          AGPT0_CON0                           Pos/Masks         Description
   ------------------------------------------------------------------------------------------------------------------------- */
#define BITP_AGPT0_CON0_SYNCBYP              15            /*  Synchronization Bypass */
#define BITP_AGPT0_CON0_RSTEN                14            /*  Counter and Prescale Reset Enable */
#define BITP_AGPT0_CON0_EVTEN                13            /*  Event Select */
#define BITP_AGPT0_CON0_EVENT                 8            /*  Event Select Range */
#define BITP_AGPT0_CON0_RLD                   7            /*  Reload Control */
#define BITP_AGPT0_CON0_CLK                   5            /*  Clock Select */
#define BITP_AGPT0_CON0_ENABLE                4            /*  Timer Enable */
#define BITP_AGPT0_CON0_MOD                   3            /*  Timer Mode */
#define BITP_AGPT0_CON0_UP                    2            /*  Count up */
#define BITP_AGPT0_CON0_PRE                   0            /*  Prescaler */
#define BITM_AGPT0_CON0_SYNCBYP              (_ADI_MSK_3(0x00008000,0x00008000U, uint16_t  ))    /*  Synchronization Bypass */
#define BITM_AGPT0_CON0_RSTEN                (_ADI_MSK_3(0x00004000,0x00004000U, uint16_t  ))    /*  Counter and Prescale Reset Enable */
#define BITM_AGPT0_CON0_EVTEN                (_ADI_MSK_3(0x00002000,0x00002000U, uint16_t  ))    /*  Event Select */
#define BITM_AGPT0_CON0_EVENT                (_ADI_MSK_3(0x00001F00,0x00001F00U, uint16_t  ))    /*  Event Select Range */
#define BITM_AGPT0_CON0_RLD                  (_ADI_MSK_3(0x00000080,0x00000080U, uint16_t  ))    /*  Reload Control */
#define BITM_AGPT0_CON0_CLK                  (_ADI_MSK_3(0x00000060,0x00000060U, uint16_t  ))    /*  Clock Select */
#define BITM_AGPT0_CON0_ENABLE               (_ADI_MSK_3(0x00000010,0x00000010U, uint16_t  ))    /*  Timer Enable */
#define BITM_AGPT0_CON0_MOD                  (_ADI_MSK_3(0x00000008,0x00000008U, uint16_t  ))    /*  Timer Mode */
#define BITM_AGPT0_CON0_UP                   (_ADI_MSK_3(0x00000004,0x00000004U, uint16_t  ))    /*  Count up */
#define BITM_AGPT0_CON0_PRE                  (_ADI_MSK_3(0x00000003,0x00000003U, uint16_t  ))    /*  Prescaler */

/* -------------------------------------------------------------------------------------------------------------------------
          AGPT0_CLRI0                          Pos/Masks         Description
   ------------------------------------------------------------------------------------------------------------------------- */
#define BITP_AGPT0_CLRI0_CAP                  1            /*  Clear Captured Event Interrupt */
#define BITP_AGPT0_CLRI0_TMOUT                0            /*  Clear Timeout Interrupt */
#define BITM_AGPT0_CLRI0_CAP                 (_ADI_MSK_3(0x00000002,0x00000002U, uint16_t  ))    /*  Clear Captured Event Interrupt */
#define BITM_AGPT0_CLRI0_TMOUT               (_ADI_MSK_3(0x00000001,0x00000001U, uint16_t  ))    /*  Clear Timeout Interrupt */

/* -------------------------------------------------------------------------------------------------------------------------
          AGPT0_CAP0                           Pos/Masks         Description
   ------------------------------------------------------------------------------------------------------------------------- */
#define BITP_AGPT0_CAP0_CAP                   0            /*  16-bit Captured Value */
#define BITM_AGPT0_CAP0_CAP                  (_ADI_MSK_3(0x0000FFFF,0x0000FFFF, int16_t   ))    /*  16-bit Captured Value */

/* -------------------------------------------------------------------------------------------------------------------------
          AGPT0_ALD0                           Pos/Masks         Description
   ------------------------------------------------------------------------------------------------------------------------- */
#define BITP_AGPT0_ALD0_ALOAD                 0            /*  Load Value, Asynchronous */
#define BITM_AGPT0_ALD0_ALOAD                (_ADI_MSK_3(0x0000FFFF,0x0000FFFF, int16_t   ))    /*  Load Value, Asynchronous */

/* -------------------------------------------------------------------------------------------------------------------------
          AGPT0_AVAL0                          Pos/Masks         Description
   ------------------------------------------------------------------------------------------------------------------------- */
#define BITP_AGPT0_AVAL0_AVAL                 0            /*  Counter Value */
#define BITM_AGPT0_AVAL0_AVAL                (_ADI_MSK_3(0x0000FFFF,0x0000FFFF, int16_t   ))    /*  Counter Value */

/* -------------------------------------------------------------------------------------------------------------------------
          AGPT0_STA0                           Pos/Masks         Description
   ------------------------------------------------------------------------------------------------------------------------- */
#define BITP_AGPT0_STA0_RSTCNT                8            /*  Counter Reset Occurring */
#define BITP_AGPT0_STA0_PDOK                  7            /*  Clear Interrupt Register Synchronization */
#define BITP_AGPT0_STA0_BUSY                  6            /*  Timer Busy */
#define BITP_AGPT0_STA0_CAP                   1            /*  Capture Event Pending */
#define BITP_AGPT0_STA0_TMOUT                 0            /*  Timeout Event Occurred */
#define BITM_AGPT0_STA0_RSTCNT               (_ADI_MSK_3(0x00000100,0x00000100U, uint16_t  ))    /*  Counter Reset Occurring */
#define BITM_AGPT0_STA0_PDOK                 (_ADI_MSK_3(0x00000080,0x00000080U, uint16_t  ))    /*  Clear Interrupt Register Synchronization */
#define BITM_AGPT0_STA0_BUSY                 (_ADI_MSK_3(0x00000040,0x00000040U, uint16_t  ))    /*  Timer Busy */
#define BITM_AGPT0_STA0_CAP                  (_ADI_MSK_3(0x00000002,0x00000002U, uint16_t  ))    /*  Capture Event Pending */
#define BITM_AGPT0_STA0_TMOUT                (_ADI_MSK_3(0x00000001,0x00000001U, uint16_t  ))    /*  Timeout Event Occurred */

/* -------------------------------------------------------------------------------------------------------------------------
          AGPT0_PWMCON0                        Pos/Masks         Description
   ------------------------------------------------------------------------------------------------------------------------- */
#define BITP_AGPT0_PWMCON0_IDLE               1            /*  PWM Idle State */
#define BITP_AGPT0_PWMCON0_MATCHEN            0            /*  PWM Match Enabled */
#define BITM_AGPT0_PWMCON0_IDLE              (_ADI_MSK_3(0x00000002,0x00000002U, uint16_t  ))    /*  PWM Idle State */
#define BITM_AGPT0_PWMCON0_MATCHEN           (_ADI_MSK_3(0x00000001,0x00000001U, uint16_t  ))    /*  PWM Match Enabled */

/* -------------------------------------------------------------------------------------------------------------------------
          AGPT0_PWMMAT0                        Pos/Masks         Description
   ------------------------------------------------------------------------------------------------------------------------- */
#define BITP_AGPT0_PWMMAT0_MATCHVAL           0            /*  PWM Match Value */
#define BITM_AGPT0_PWMMAT0_MATCHVAL          (_ADI_MSK_3(0x0000FFFF,0x0000FFFF, int16_t   ))    /*  PWM Match Value */

/* -------------------------------------------------------------------------------------------------------------------------
          AGPT0_INTEN                          Pos/Masks         Description
   ------------------------------------------------------------------------------------------------------------------------- */
#define BITP_AGPT0_INTEN_INTEN                0            /*  Interrupt Enable */
#define BITM_AGPT0_INTEN_INTEN               (_ADI_MSK_3(0x00000001,0x00000001U, uint16_t  ))    /*  Interrupt Enable */


/* ============================================================================================================================
        General Purpose Timer
   ============================================================================================================================ */

/* ============================================================================================================================
        AGPT1
   ============================================================================================================================ */
#define REG_AGPT1_LD1                        0x00000E00            /*  AGPT1 16-bit Load Value Register */
#define REG_AGPT1_VAL1                       0x00000E04            /*  AGPT1 16-bit Timer Value Register */
#define REG_AGPT1_CON1                       0x00000E08            /*  AGPT1 Control Register */
#define REG_AGPT1_CLRI1                      0x00000E0C            /*  AGPT1 Clear Interrupt Register */
#define REG_AGPT1_CAP1                       0x00000E10            /*  AGPT1 Capture Register */
#define REG_AGPT1_ALD1                       0x00000E14            /*  AGPT1 16-bit Load Value, Asynchronous Register */
#define REG_AGPT1_AVAL1                      0x00000E18            /*  AGPT1 16-bit Timer Value, Asynchronous Register */
#define REG_AGPT1_STA1                       0x00000E1C            /*  AGPT1 Status Register */
#define REG_AGPT1_PWMCON1                    0x00000E20            /*  AGPT1 PWM Control Register */
#define REG_AGPT1_PWMMAT1                    0x00000E24            /*  AGPT1 PWM Match Value Register */
#define REG_AGPT1_INTEN1                     0x00000E28            /*  AGPT1 Interrupt Enable */

/* ============================================================================================================================
        AGPT1 Register BitMasks, Positions & Enumerations 
   ============================================================================================================================ */
/* -------------------------------------------------------------------------------------------------------------------------
          AGPT1_LD1                            Pos/Masks         Description
   ------------------------------------------------------------------------------------------------------------------------- */
#define BITP_AGPT1_LD1_LOAD                   0            /*  Load Value */
#define BITM_AGPT1_LD1_LOAD                  (_ADI_MSK_3(0x0000FFFF,0x0000FFFF, int16_t   ))    /*  Load Value */

/* -------------------------------------------------------------------------------------------------------------------------
          AGPT1_VAL1                           Pos/Masks         Description
   ------------------------------------------------------------------------------------------------------------------------- */
#define BITP_AGPT1_VAL1_VAL                   0            /*  Current Count */
#define BITM_AGPT1_VAL1_VAL                  (_ADI_MSK_3(0x0000FFFF,0x0000FFFF, int16_t   ))    /*  Current Count */

/* -------------------------------------------------------------------------------------------------------------------------
          AGPT1_CON1                           Pos/Masks         Description
   ------------------------------------------------------------------------------------------------------------------------- */
#define BITP_AGPT1_CON1_SYNCBYP              15            /*  Synchronization Bypass */
#define BITP_AGPT1_CON1_RSTEN                14            /*  Counter and Prescale Reset Enable */
#define BITP_AGPT1_CON1_EVENTEN              13            /*  Event Select */
#define BITP_AGPT1_CON1_EVENT                 8            /*  Event Select Range */
#define BITP_AGPT1_CON1_RLD                   7            /*  Reload Control */
#define BITP_AGPT1_CON1_CLK                   5            /*  Clock Select */
#define BITP_AGPT1_CON1_ENABLE                4            /*  Timer Enable */
#define BITP_AGPT1_CON1_MOD                   3            /*  Timer Mode */
#define BITP_AGPT1_CON1_UP                    2            /*  Count up */
#define BITP_AGPT1_CON1_PRE                   0            /*  Prescaler */
#define BITM_AGPT1_CON1_SYNCBYP              (_ADI_MSK_3(0x00008000,0x00008000U, uint16_t  ))    /*  Synchronization Bypass */
#define BITM_AGPT1_CON1_RSTEN                (_ADI_MSK_3(0x00004000,0x00004000U, uint16_t  ))    /*  Counter and Prescale Reset Enable */
#define BITM_AGPT1_CON1_EVENTEN              (_ADI_MSK_3(0x00002000,0x00002000U, uint16_t  ))    /*  Event Select */
#define BITM_AGPT1_CON1_EVENT                (_ADI_MSK_3(0x00001F00,0x00001F00U, uint16_t  ))    /*  Event Select Range */
#define BITM_AGPT1_CON1_RLD                  (_ADI_MSK_3(0x00000080,0x00000080U, uint16_t  ))    /*  Reload Control */
#define BITM_AGPT1_CON1_CLK                  (_ADI_MSK_3(0x00000060,0x00000060U, uint16_t  ))    /*  Clock Select */
#define BITM_AGPT1_CON1_ENABLE               (_ADI_MSK_3(0x00000010,0x00000010U, uint16_t  ))    /*  Timer Enable */
#define BITM_AGPT1_CON1_MOD                  (_ADI_MSK_3(0x00000008,0x00000008U, uint16_t  ))    /*  Timer Mode */
#define BITM_AGPT1_CON1_UP                   (_ADI_MSK_3(0x00000004,0x00000004U, uint16_t  ))    /*  Count up */
#define BITM_AGPT1_CON1_PRE                  (_ADI_MSK_3(0x00000003,0x00000003U, uint16_t  ))    /*  Prescaler */

/* -------------------------------------------------------------------------------------------------------------------------
          AGPT1_CLRI1                          Pos/Masks         Description
   ------------------------------------------------------------------------------------------------------------------------- */
#define BITP_AGPT1_CLRI1_CAP                  1            /*  Clear Captured Event Interrupt */
#define BITP_AGPT1_CLRI1_TMOUT                0            /*  Clear Timeout Interrupt */
#define BITM_AGPT1_CLRI1_CAP                 (_ADI_MSK_3(0x00000002,0x00000002U, uint16_t  ))    /*  Clear Captured Event Interrupt */
#define BITM_AGPT1_CLRI1_TMOUT               (_ADI_MSK_3(0x00000001,0x00000001U, uint16_t  ))    /*  Clear Timeout Interrupt */

/* -------------------------------------------------------------------------------------------------------------------------
          AGPT1_CAP1                           Pos/Masks         Description
   ------------------------------------------------------------------------------------------------------------------------- */
#define BITP_AGPT1_CAP1_CAP                   0            /*  16-bit Captured Value. */
#define BITM_AGPT1_CAP1_CAP                  (_ADI_MSK_3(0x0000FFFF,0x0000FFFF, int16_t   ))    /*  16-bit Captured Value. */

/* -------------------------------------------------------------------------------------------------------------------------
          AGPT1_ALD1                           Pos/Masks         Description
   ------------------------------------------------------------------------------------------------------------------------- */
#define BITP_AGPT1_ALD1_ALOAD                 0            /*  Load Value, Asynchronous */
#define BITM_AGPT1_ALD1_ALOAD                (_ADI_MSK_3(0x0000FFFF,0x0000FFFF, int16_t   ))    /*  Load Value, Asynchronous */

/* -------------------------------------------------------------------------------------------------------------------------
          AGPT1_AVAL1                          Pos/Masks         Description
   ------------------------------------------------------------------------------------------------------------------------- */
#define BITP_AGPT1_AVAL1_AVAL                 0            /*  Counter Value */
#define BITM_AGPT1_AVAL1_AVAL                (_ADI_MSK_3(0x0000FFFF,0x0000FFFF, int16_t   ))    /*  Counter Value */

/* -------------------------------------------------------------------------------------------------------------------------
          AGPT1_STA1                           Pos/Masks         Description
   ------------------------------------------------------------------------------------------------------------------------- */
#define BITP_AGPT1_STA1_RSTCNT                8            /*  Counter Reset Occurring */
#define BITP_AGPT1_STA1_PDOK                  7            /*  Clear Interrupt Register Synchronization */
#define BITP_AGPT1_STA1_BUSY                  6            /*  Timer Busy */
#define BITP_AGPT1_STA1_CAP                   1            /*  Capture Event Pending */
#define BITP_AGPT1_STA1_TMOUT                 0            /*  Timeout Event Occurred */
#define BITM_AGPT1_STA1_RSTCNT               (_ADI_MSK_3(0x00000100,0x00000100U, uint16_t  ))    /*  Counter Reset Occurring */
#define BITM_AGPT1_STA1_PDOK                 (_ADI_MSK_3(0x00000080,0x00000080U, uint16_t  ))    /*  Clear Interrupt Register Synchronization */
#define BITM_AGPT1_STA1_BUSY                 (_ADI_MSK_3(0x00000040,0x00000040U, uint16_t  ))    /*  Timer Busy */
#define BITM_AGPT1_STA1_CAP                  (_ADI_MSK_3(0x00000002,0x00000002U, uint16_t  ))    /*  Capture Event Pending */
#define BITM_AGPT1_STA1_TMOUT                (_ADI_MSK_3(0x00000001,0x00000001U, uint16_t  ))    /*  Timeout Event Occurred */

/* -------------------------------------------------------------------------------------------------------------------------
          AGPT1_PWMCON1                        Pos/Masks         Description
   ------------------------------------------------------------------------------------------------------------------------- */
#define BITP_AGPT1_PWMCON1_IDLE               1            /*  PWM Idle State. */
#define BITP_AGPT1_PWMCON1_MATCHEN            0            /*  PWM Match Enabled. */
#define BITM_AGPT1_PWMCON1_IDLE              (_ADI_MSK_3(0x00000002,0x00000002U, uint16_t  ))    /*  PWM Idle State. */
#define BITM_AGPT1_PWMCON1_MATCHEN           (_ADI_MSK_3(0x00000001,0x00000001U, uint16_t  ))    /*  PWM Match Enabled. */

/* -------------------------------------------------------------------------------------------------------------------------
          AGPT1_PWMMAT1                        Pos/Masks         Description
   ------------------------------------------------------------------------------------------------------------------------- */
#define BITP_AGPT1_PWMMAT1_MATCHVAL           0            /*  PWM Match Value */
#define BITM_AGPT1_PWMMAT1_MATCHVAL          (_ADI_MSK_3(0x0000FFFF,0x0000FFFF, int16_t   ))    /*  PWM Match Value */

/* -------------------------------------------------------------------------------------------------------------------------
          AGPT1_INTEN1                         Pos/Masks         Description
   ------------------------------------------------------------------------------------------------------------------------- */
#define BITP_AGPT1_INTEN1_INTEN               0            /*  Interrupt Enable */
#define BITM_AGPT1_INTEN1_INTEN              (_ADI_MSK_3(0x00000001,0x00000001U, uint16_t  ))    /*  Interrupt Enable */


/* ============================================================================================================================
        CRC Accelerator
   ============================================================================================================================ */

/* ============================================================================================================================
        AFECRC
   ============================================================================================================================ */
#define REG_AFECRC_CTL                       0x00001000            /*  AFECRC CRC Control Register */
#define REG_AFECRC_IPDATA                    0x00001004            /*  AFECRC Data Input. */
#define REG_AFECRC_RESULT                    0x00001008            /*  AFECRC CRC Residue */
#define REG_AFECRC_POLY                      0x0000100C            /*  AFECRC CRC Reduction Polynomial */
#define REG_AFECRC_IPBITS                    0x00001010            /*  AFECRC Input Data Bits */
#define REG_AFECRC_IPBYTE                    0x00001014            /*  AFECRC Input Data Byte */
#define REG_AFECRC_CRC_SIG_COMP              0x00001020            /*  AFECRC CRC Signature Compare Data Input. */
#define REG_AFECRC_CRCINTEN                  0x00001024            /*  AFECRC CRC Error Interrupt Enable Bit */
#define REG_AFECRC_INTSTA                    0x00001028            /*  AFECRC CRC Error Interrupt Status Bit */

/* ============================================================================================================================
        AFECRC Register BitMasks, Positions & Enumerations 
   ============================================================================================================================ */
/* -------------------------------------------------------------------------------------------------------------------------
          AFECRC_CTL                           Pos/Masks         Description
   ------------------------------------------------------------------------------------------------------------------------- */
#define BITP_AFECRC_CTL_REVID                28            /*  Revision ID */
#define BITP_AFECRC_CTL_MON_EN                9            /*  Enable Apb32/Apb16 to Get Address/Data for CRC Calculation */
#define BITP_AFECRC_CTL_W16SWP                4            /*  Word16 Swap Enabled. */
#define BITP_AFECRC_CTL_BYTMIRR               3            /*  Byte Mirroring. */
#define BITP_AFECRC_CTL_BITMIRR               2            /*  Bit Mirroring. */
#define BITP_AFECRC_CTL_LSBFIRST              1            /*  LSB First Calculation Order */
#define BITP_AFECRC_CTL_EN                    0            /*  CRC Peripheral Enable */
#define BITM_AFECRC_CTL_REVID                (_ADI_MSK_3(0xF0000000,0xF0000000UL, uint32_t  ))    /*  Revision ID */
#define BITM_AFECRC_CTL_MON_EN               (_ADI_MSK_3(0x00000200,0x00000200UL, uint32_t  ))    /*  Enable Apb32/Apb16 to Get Address/Data for CRC Calculation */
#define BITM_AFECRC_CTL_W16SWP               (_ADI_MSK_3(0x00000010,0x00000010UL, uint32_t  ))    /*  Word16 Swap Enabled. */
#define BITM_AFECRC_CTL_BYTMIRR              (_ADI_MSK_3(0x00000008,0x00000008UL, uint32_t  ))    /*  Byte Mirroring. */
#define BITM_AFECRC_CTL_BITMIRR              (_ADI_MSK_3(0x00000004,0x00000004UL, uint32_t  ))    /*  Bit Mirroring. */
#define BITM_AFECRC_CTL_LSBFIRST             (_ADI_MSK_3(0x00000002,0x00000002UL, uint32_t  ))    /*  LSB First Calculation Order */
#define BITM_AFECRC_CTL_EN                   (_ADI_MSK_3(0x00000001,0x00000001UL, uint32_t  ))    /*  CRC Peripheral Enable */

/* -------------------------------------------------------------------------------------------------------------------------
          AFECRC_IPDATA                        Pos/Masks         Description
   ------------------------------------------------------------------------------------------------------------------------- */
#define BITP_AFECRC_IPDATA_VALUE              0            /*  Data Input. */
#define BITM_AFECRC_IPDATA_VALUE             (_ADI_MSK_3(0xFFFFFFFF,0xFFFFFFFF, int32_t   ))    /*  Data Input. */

/* -------------------------------------------------------------------------------------------------------------------------
          AFECRC_RESULT                        Pos/Masks         Description
   ------------------------------------------------------------------------------------------------------------------------- */
#define BITP_AFECRC_RESULT_VALUE              0            /*  CRC Residue */
#define BITM_AFECRC_RESULT_VALUE             (_ADI_MSK_3(0xFFFFFFFF,0xFFFFFFFF, int32_t   ))    /*  CRC Residue */

/* -------------------------------------------------------------------------------------------------------------------------
          AFECRC_POLY                          Pos/Masks         Description
   ------------------------------------------------------------------------------------------------------------------------- */
#define BITP_AFECRC_POLY_VALUE                0            /*  CRC Reduction Polynomial */
#define BITM_AFECRC_POLY_VALUE               (_ADI_MSK_3(0xFFFFFFFF,0xFFFFFFFFUL, uint32_t  ))    /*  CRC Reduction Polynomial */

/* -------------------------------------------------------------------------------------------------------------------------
          AFECRC_IPBITS                        Pos/Masks         Description
   ------------------------------------------------------------------------------------------------------------------------- */
#define BITP_AFECRC_IPBITS_DATA_BITS          0            /*  Input Data Bits. */
#define BITM_AFECRC_IPBITS_DATA_BITS         (_ADI_MSK_3(0x000000FF,0x000000FFU, uint8_t   ))    /*  Input Data Bits. */

/* -------------------------------------------------------------------------------------------------------------------------
          AFECRC_IPBYTE                        Pos/Masks         Description
   ------------------------------------------------------------------------------------------------------------------------- */
#define BITP_AFECRC_IPBYTE_DATA_BYTE          0            /*  Input Data Byte. */
#define BITM_AFECRC_IPBYTE_DATA_BYTE         (_ADI_MSK_3(0x000000FF,0x000000FFU, uint8_t   ))    /*  Input Data Byte. */

/* -------------------------------------------------------------------------------------------------------------------------
          AFECRC_CRC_SIG_COMP                  Pos/Masks         Description
   ------------------------------------------------------------------------------------------------------------------------- */
#define BITP_AFECRC_CRC_SIG_COMP_CRC_SIG      0            /*  CRC Signature Compare Data Input. */
#define BITM_AFECRC_CRC_SIG_COMP_CRC_SIG     (_ADI_MSK_3(0xFFFFFFFF,0xFFFFFFFFUL, uint32_t  ))    /*  CRC Signature Compare Data Input. */

/* -------------------------------------------------------------------------------------------------------------------------
          AFECRC_CRCINTEN                      Pos/Masks         Description
   ------------------------------------------------------------------------------------------------------------------------- */
#define BITP_AFECRC_CRCINTEN_RESERVED_31_1    1            /*  Reserved */
#define BITP_AFECRC_CRCINTEN_CRC_ERR_EN       0            /*  CRC Error Interrupt Enable Bit */
#define BITM_AFECRC_CRCINTEN_RESERVED_31_1   (_ADI_MSK_3(0xFFFFFFFE,0xFFFFFFFEUL, uint32_t  ))    /*  Reserved */
#define BITM_AFECRC_CRCINTEN_CRC_ERR_EN      (_ADI_MSK_3(0x00000001,0x00000001UL, uint32_t  ))    /*  CRC Error Interrupt Enable Bit */

/* -------------------------------------------------------------------------------------------------------------------------
          AFECRC_INTSTA                        Pos/Masks         Description
   ------------------------------------------------------------------------------------------------------------------------- */
#define BITP_AFECRC_INTSTA_CRC_ERR_ST         0            /*  CRC Error Interrupt Status Bit */
#define BITM_AFECRC_INTSTA_CRC_ERR_ST        (_ADI_MSK_3(0x00000001,0x00000001UL, uint32_t  ))    /*  CRC Error Interrupt Status Bit */


/* ============================================================================================================================
        
   ============================================================================================================================ */

/* ============================================================================================================================
        AFE
   ============================================================================================================================ */
#define REG_AFE_AFECON_RESET                 0x00080000            /*      Reset Value for AFECON  */
#define REG_AFE_AFECON                       0x00002000            /*  AFE AFE Configuration */
#define REG_AFE_SEQCON_RESET                 0x00000002            /*      Reset Value for SEQCON  */
#define REG_AFE_SEQCON                       0x00002004            /*  AFE Sequencer Configuration */
#define REG_AFE_FIFOCON_RESET                0x00001010            /*      Reset Value for FIFOCON  */
#define REG_AFE_FIFOCON                      0x00002008            /*  AFE FIFOs Configuration */
#define REG_AFE_SWCON_RESET                  0x0000FFFF            /*      Reset Value for SWCON  */
#define REG_AFE_SWCON                        0x0000200C            /*  AFE Switch Matrix Configuration */
#define REG_AFE_HSDACCON_RESET               0x0000001E            /*      Reset Value for HSDACCON  */
#define REG_AFE_HSDACCON                     0x00002010            /*  AFE High Speed DAC Configuration */
#define REG_AFE_WGCON_RESET                  0x00000030            /*      Reset Value for WGCON  */
#define REG_AFE_WGCON                        0x00002014            /*  AFE Waveform Generator Configuration */
#define REG_AFE_WGDCLEVEL1_RESET             0x00000000            /*      Reset Value for WGDCLEVEL1  */
#define REG_AFE_WGDCLEVEL1                   0x00002018            /*  AFE Waveform Generator - Trapezoid DC Level 1 */
#define REG_AFE_WGDCLEVEL2_RESET             0x00000000            /*      Reset Value for WGDCLEVEL2  */
#define REG_AFE_WGDCLEVEL2                   0x0000201C            /*  AFE Waveform Generator - Trapezoid DC Level 2 */
#define REG_AFE_WGDELAY1_RESET               0x00000000            /*      Reset Value for WGDELAY1  */
#define REG_AFE_WGDELAY1                     0x00002020            /*  AFE Waveform Generator - Trapezoid Delay 1 Time */
#define REG_AFE_WGSLOPE1_RESET               0x00000000            /*      Reset Value for WGSLOPE1  */
#define REG_AFE_WGSLOPE1                     0x00002024            /*  AFE Waveform Generator - Trapezoid Slope 1 Time */
#define REG_AFE_WGDELAY2_RESET               0x00000000            /*      Reset Value for WGDELAY2  */
#define REG_AFE_WGDELAY2                     0x00002028            /*  AFE Waveform Generator - Trapezoid Delay 2 Time */
#define REG_AFE_WGSLOPE2_RESET               0x00000000            /*      Reset Value for WGSLOPE2  */
#define REG_AFE_WGSLOPE2                     0x0000202C            /*  AFE Waveform Generator - Trapezoid Slope 2 Time */
#define REG_AFE_WGFCW_RESET                  0x00000000            /*      Reset Value for WGFCW  */
#define REG_AFE_WGFCW                        0x00002030            /*  AFE Waveform Generator - Sinusoid Frequency Control Word */
#define REG_AFE_WGPHASE_RESET                0x00000000            /*      Reset Value for WGPHASE  */
#define REG_AFE_WGPHASE                      0x00002034            /*  AFE Waveform Generator - Sinusoid Phase Offset */
#define REG_AFE_WGOFFSET_RESET               0x00000000            /*      Reset Value for WGOFFSET  */
#define REG_AFE_WGOFFSET                     0x00002038            /*  AFE Waveform Generator - Sinusoid Offset */
#define REG_AFE_WGAMPLITUDE_RESET            0x00000000            /*      Reset Value for WGAMPLITUDE  */
#define REG_AFE_WGAMPLITUDE                  0x0000203C            /*  AFE Waveform Generator - Sinusoid Amplitude */
#define REG_AFE_ADCFILTERCON_RESET           0x00000301            /*      Reset Value for ADCFILTERCON  */
#define REG_AFE_ADCFILTERCON                 0x00002044            /*  AFE ADC Output Filters Configuration */
#define REG_AFE_HSDACDAT_RESET               0x00000800            /*      Reset Value for HSDACDAT  */
#define REG_AFE_HSDACDAT                     0x00002048            /*  AFE HS DAC Code */
#define REG_AFE_LPREFBUFCON_RESET            0x00000000            /*      Reset Value for LPREFBUFCON  */
#define REG_AFE_LPREFBUFCON                  0x00002050            /*  AFE LPREF_BUF_CON */
#define REG_AFE_SYNCEXTDEVICE_RESET          0x00000000            /*      Reset Value for SYNCEXTDEVICE  */
#define REG_AFE_SYNCEXTDEVICE                0x00002054            /*  AFE SYNC External Devices */
#define REG_AFE_SEQCRC_RESET                 0x00000001            /*      Reset Value for SEQCRC  */
#define REG_AFE_SEQCRC                       0x00002060            /*  AFE Sequencer CRC Value */
#define REG_AFE_SEQCNT_RESET                 0x00000000            /*      Reset Value for SEQCNT  */
#define REG_AFE_SEQCNT                       0x00002064            /*  AFE Sequencer Command Count */
#define REG_AFE_SEQTIMEOUT_RESET             0x00000000            /*      Reset Value for SEQTIMEOUT  */
#define REG_AFE_SEQTIMEOUT                   0x00002068            /*  AFE Sequencer Timeout Counter */
#define REG_AFE_DATAFIFORD_RESET             0x00000000            /*      Reset Value for DATAFIFORD  */
#define REG_AFE_DATAFIFORD                   0x0000206C            /*  AFE Data FIFO Read */
#define REG_AFE_CMDFIFOWRITE_RESET           0x00000000            /*      Reset Value for CMDFIFOWRITE  */
#define REG_AFE_CMDFIFOWRITE                 0x00002070            /*  AFE Command FIFO Write */
#define REG_AFE_ADCDAT_RESET                 0x00000000            /*      Reset Value for ADCDAT  */
#define REG_AFE_ADCDAT                       0x00002074            /*  AFE ADC Raw Result */
#define REG_AFE_DFTREAL_RESET                0x00000000            /*      Reset Value for DFTREAL  */
#define REG_AFE_DFTREAL                      0x00002078            /*  AFE DFT Result, Real Part */
#define REG_AFE_DFTIMAG_RESET                0x00000000            /*      Reset Value for DFTIMAG  */
#define REG_AFE_DFTIMAG                      0x0000207C            /*  AFE DFT Result, Imaginary Part */
#define REG_AFE_SINC2DAT_RESET               0x00000000            /*      Reset Value for SINC2DAT  */
#define REG_AFE_SINC2DAT                     0x00002080            /*  AFE Supply Rejection Filter Result */
#define REG_AFE_TEMPSENSDAT_RESET            0x00000000            /*      Reset Value for TEMPSENSDAT  */
#define REG_AFE_TEMPSENSDAT                  0x00002084            /*  AFE Temperature Sensor Result */
#define REG_AFE_AFEGENINTSTA_RESET           0x00000000            /*      Reset Value for AFEGENINTSTA  */
#define REG_AFE_AFEGENINTSTA                 0x0000209C            /*  AFE Analog Generation Interrupt */
#define REG_AFE_ADCMIN_RESET                 0x00000000            /*      Reset Value for ADCMIN  */
#define REG_AFE_ADCMIN                       0x000020A8            /*  AFE ADC Minimum Value Check */
#define REG_AFE_ADCMINSM_RESET               0x00000000            /*      Reset Value for ADCMINSM  */
#define REG_AFE_ADCMINSM                     0x000020AC            /*  AFE ADCMIN Hysteresis Value */
#define REG_AFE_ADCMAX_RESET                 0x00000000            /*      Reset Value for ADCMAX  */
#define REG_AFE_ADCMAX                       0x000020B0            /*  AFE ADC Maximum Value Check */
#define REG_AFE_ADCMAXSMEN_RESET             0x00000000            /*      Reset Value for ADCMAXSMEN  */
#define REG_AFE_ADCMAXSMEN                   0x000020B4            /*  AFE ADCMAX Hysteresis Value */
#define REG_AFE_ADCDELTA_RESET               0x00000000            /*      Reset Value for ADCDELTA  */
#define REG_AFE_ADCDELTA                     0x000020B8            /*  AFE ADC Delta Value */
#define REG_AFE_HPOSCCON_RESET               0x00000024            /*      Reset Value for HPOSCCON  */
#define REG_AFE_HPOSCCON                     0x000020BC            /*  AFE HPOSC Configuration */
#define REG_AFE_DFTCON_RESET                 0x00000090            /*      Reset Value for DFTCON  */
#define REG_AFE_DFTCON                       0x000020D0            /*  AFE AFE DSP Configuration */
#define REG_AFE_LPTIASW1                     0x000020E0            /*  AFE ULPTIA Switch Configuration for Channel 1 */
#define REG_AFE_LPTIASW0_RESET               0x00000000            /*      Reset Value for LPTIASW0  */
#define REG_AFE_LPTIACON1                    0x000020E8            /*  AFE ULPTIA Control Bits Channel 1 */
#define REG_AFE_LPTIASW0                     0x000020E4            /*  AFE ULPTIA Switch Configuration for Channel 0 */
#define REG_AFE_LPTIACON0_RESET              0x00000003            /*      Reset Value for LPTIACON0  */
#define REG_AFE_LPTIACON0                    0x000020EC            /*  AFE ULPTIA Control Bits Channel 0 */
#define REG_AFE_HSRTIACON_RESET              0x0000000F            /*      Reset Value for HSRTIACON  */
#define REG_AFE_HSRTIACON                    0x000020F0            /*  AFE High Power RTIA Configuration */
#define REG_AFE_DE1RESCON                    0x000020F4            /*  AFE DE1 HSTIA Resistors Configuration */
#define REG_AFE_DE0RESCON_RESET              0x000000FF            /*      Reset Value for DE0RESCON  */
#define REG_AFE_DE0RESCON                    0x000020F8            /*  AFE DE0 HSTIA Resistors Configuration */
#define REG_AFE_HSTIACON_RESET               0x00000000            /*      Reset Value for HSTIACON  */
#define REG_AFE_HSTIACON                     0x000020FC            /*  AFE HSTIA Amplifier Configuration */
#define REG_AFE_LPMODEKEY_RESET             0x00000000            /*      Reset Value for LPMODEKEY  */
#define REG_AFE_LPMODEKEY                   0x0000210C            /*  AFE LP Mode AFE Control Lock */
#define REG_AFE_LPMODECLKSEL_RESET          0x00000000            /*      Reset Value for LPMODECLKSEL  */
#define REG_AFE_LPMODECLKSEL                0x00002110            /*  AFE LFSYSCLKEN */
#define REG_AFE_LPMODECON_RESET             0x00000102            /*      Reset Value for LPMODECON  */
#define REG_AFE_LPMODECON                   0x00002114            /*  AFE LPMODECON */
#define REG_AFE_SEQSLPLOCK_RESET             0x00000000            /*      Reset Value for SEQSLPLOCK  */
#define REG_AFE_SEQSLPLOCK                   0x00002118            /*  AFE Sequencer Sleep Control Lock */
#define REG_AFE_SEQTRGSLP_RESET              0x00000000            /*      Reset Value for SEQTRGSLP  */
#define REG_AFE_SEQTRGSLP                    0x0000211C            /*  AFE Sequencer Trigger Sleep */
#define REG_AFE_LPDACDAT0_RESET              0x00000000            /*      Reset Value for LPDACDAT0  */
#define REG_AFE_LPDACDAT0                    0x00002120            /*  AFE LPDAC Data-out */
#define REG_AFE_LPDACSW0_RESET               0x00000000            /*      Reset Value for LPDACSW0  */
#define REG_AFE_LPDACSW0                     0x00002124            /*  AFE LPDAC0 Switch Control */
#define REG_AFE_LPDACCON0_RESET              0x00000002            /*      Reset Value for LPDACCON0  */
#define REG_AFE_LPDACCON0                    0x00002128            /*  AFE LPDAC Control Bits */
#define REG_AFE_LPDACDAT1                    0x0000212C            /*  AFE Low Power DAC1 data register */
#define REG_AFE_LPDACSW1                     0x00002130            /*  AFE Control register for switches to LPDAC1 */
#define REG_AFE_LPDACCON1                    0x00002134            /*  AFE ULP_DACCON1 */
#define REG_AFE_DSWFULLCON_RESET             0x00000000            /*      Reset Value for DSWFULLCON  */
#define REG_AFE_DSWFULLCON                   0x00002150            /*  AFE Switch Matrix Full Configuration (D) */
#define REG_AFE_NSWFULLCON_RESET             0x00000000            /*      Reset Value for NSWFULLCON  */
#define REG_AFE_NSWFULLCON                   0x00002154            /*  AFE Switch Matrix Full Configuration (N) */
#define REG_AFE_PSWFULLCON_RESET             0x00000000            /*      Reset Value for PSWFULLCON  */
#define REG_AFE_PSWFULLCON                   0x00002158            /*  AFE Switch Matrix Full Configuration (P) */
#define REG_AFE_TSWFULLCON_RESET             0x00000000            /*      Reset Value for TSWFULLCON  */
#define REG_AFE_TSWFULLCON                   0x0000215C            /*  AFE Switch Matrix Full Configuration (T) */
#define REG_AFE_TEMPSENS_RESET               0x00000000            /*      Reset Value for TEMPSENS  */
#define REG_AFE_TEMPSENS                     0x00002174            /*  AFE Temp Sensor Configuration */
#define REG_AFE_BUFSENCON_RESET              0x00000037            /*      Reset Value for BUFSENCON  */
#define REG_AFE_BUFSENCON                    0x00002180            /*  AFE HP and LP Buffer Control */
#define REG_AFE_ADCCON_RESET                 0x00000000            /*      Reset Value for ADCCON  */
#define REG_AFE_ADCCON                       0x000021A8            /*  AFE ADC Configuration */
#define REG_AFE_DSWSTA_RESET                 0x00000000            /*      Reset Value for DSWSTA  */
#define REG_AFE_DSWSTA                       0x000021B0            /*  AFE Switch Matrix Status (D) */
#define REG_AFE_PSWSTA_RESET                 0x00006000            /*      Reset Value for PSWSTA  */
#define REG_AFE_PSWSTA                       0x000021B4            /*  AFE Switch Matrix Status (P) */
#define REG_AFE_NSWSTA_RESET                 0x00000C00            /*      Reset Value for NSWSTA  */
#define REG_AFE_NSWSTA                       0x000021B8            /*  AFE Switch Matrix Status (N) */
#define REG_AFE_TSWSTA_RESET                 0x00000000            /*      Reset Value for TSWSTA  */
#define REG_AFE_TSWSTA                       0x000021BC            /*  AFE Switch Matrix Status (T) */
#define REG_AFE_STATSVAR_RESET               0x00000000            /*      Reset Value for STATSVAR  */
#define REG_AFE_STATSVAR                     0x000021C0            /*  AFE Variance Output */
#define REG_AFE_STATSCON_RESET               0x00000000            /*      Reset Value for STATSCON  */
#define REG_AFE_STATSCON                     0x000021C4            /*  AFE Statistics Control */
#define REG_AFE_STATSMEAN_RESET              0x00000000            /*      Reset Value for STATSMEAN  */
#define REG_AFE_STATSMEAN                    0x000021C8            /*  AFE Statistics Mean Output */
#define REG_AFE_SEQ0INFO_RESET               0x00000000            /*      Reset Value for SEQ0INFO  */
#define REG_AFE_SEQ0INFO                     0x000021CC            /*  AFE Sequence 0 Info */
#define REG_AFE_SEQ2INFO_RESET               0x00000000            /*      Reset Value for SEQ2INFO  */
#define REG_AFE_SEQ2INFO                     0x000021D0            /*  AFE Sequence 2 Info */
#define REG_AFE_CMDFIFOWADDR_RESET           0x00000000            /*      Reset Value for CMDFIFOWADDR  */
#define REG_AFE_CMDFIFOWADDR                 0x000021D4            /*  AFE Command FIFO Write Address */
#define REG_AFE_CMDDATACON_RESET             0x00000410            /*      Reset Value for CMDDATACON  */
#define REG_AFE_CMDDATACON                   0x000021D8            /*  AFE Command Data Control */
#define REG_AFE_DATAFIFOTHRES_RESET          0x00000000            /*      Reset Value for DATAFIFOTHRES  */
#define REG_AFE_DATAFIFOTHRES                0x000021E0            /*  AFE Data FIFO Threshold */
#define REG_AFE_SEQ3INFO_RESET               0x00000000            /*      Reset Value for SEQ3INFO  */
#define REG_AFE_SEQ3INFO                     0x000021E4            /*  AFE Sequence 3 Info */
#define REG_AFE_SEQ1INFO_RESET               0x00000000            /*      Reset Value for SEQ1INFO  */
#define REG_AFE_SEQ1INFO                     0x000021E8            /*  AFE Sequence 1 Info */
#define REG_AFE_REPEATADCCNV_RESET           0x00000160            /*      Reset Value for REPEATADCCNV  */
#define REG_AFE_REPEATADCCNV                 0x000021F0            /*  AFE REPEAT ADC Conversions */
#define REG_AFE_FIFOCNTSTA_RESET             0x00000000            /*      Reset Value for FIFOCNTSTA  */
#define REG_AFE_FIFOCNTSTA                   0x00002200            /*  AFE CMD and DATA FIFO INTERNAL DATA COUNT */
#define REG_AFE_CALDATLOCK_RESET             0x00000000            /*      Reset Value for CALDATLOCK  */
#define REG_AFE_CALDATLOCK                   0x00002230            /*  AFE Calibration Data Lock */
#define REG_AFE_ADCOFFSETHSTIA_RESET         0x00000000            /*      Reset Value for ADCOFFSETHSTIA  */
#define REG_AFE_ADCOFFSETHSTIA               0x00002234            /*  AFE ADC Offset Calibration High Speed TIA Channel */
#define REG_AFE_ADCGAINTEMPSENS0_RESET       0x00004000            /*      Reset Value for ADCGAINTEMPSENS0  */
#define REG_AFE_ADCGAINTEMPSENS0             0x00002238            /*  AFE ADC Gain Calibration Temp Sensor Channel */
#define REG_AFE_ADCOFFSETTEMPSENS0_RESET     0x00000000            /*      Reset Value for ADCOFFSETTEMPSENS0  */
#define REG_AFE_ADCOFFSETTEMPSENS0           0x0000223C            /*  AFE ADC Offset Calibration Temp Sensor Channel 0 */
#define REG_AFE_ADCGAINGN1_RESET             0x00004000            /*      Reset Value for ADCGAINGN1  */
#define REG_AFE_ADCGAINGN1                   0x00002240            /*  AFE ADCPGAGN1: ADC Gain Calibration Auxiliary Input Channel */
#define REG_AFE_ADCOFFSETGN1_RESET           0x00000000            /*      Reset Value for ADCOFFSETGN1  */
#define REG_AFE_ADCOFFSETGN1                 0x00002244            /*  AFE ADC Offset Calibration Auxiliary Channel (PGA Gain=1) */
#define REG_AFE_DACGAIN_RESET                0x00000800            /*      Reset Value for DACGAIN  */
#define REG_AFE_DACGAIN                      0x00002260            /*  AFE DACGAIN */
#define REG_AFE_DACOFFSETATTEN_RESET         0x00000000            /*      Reset Value for DACOFFSETATTEN  */
#define REG_AFE_DACOFFSETATTEN               0x00002264            /*  AFE DAC Offset with Attenuator Enabled (LP Mode) */
#define REG_AFE_DACOFFSET_RESET              0x00000000            /*      Reset Value for DACOFFSET  */
#define REG_AFE_DACOFFSET                    0x00002268            /*  AFE DAC Offset with Attenuator Disabled (LP Mode) */
#define REG_AFE_ADCGAINGN1P5_RESET           0x00004000            /*      Reset Value for ADCGAINGN1P5  */
#define REG_AFE_ADCGAINGN1P5                 0x00002270            /*  AFE ADC Gain Calibration Auxiliary Input Channel (PGA Gain=1.5) */
#define REG_AFE_ADCGAINGN2_RESET             0x00004000            /*      Reset Value for ADCGAINGN2  */
#define REG_AFE_ADCGAINGN2                   0x00002274            /*  AFE ADC Gain Calibration Auxiliary Input Channel (PGA Gain=2) */
#define REG_AFE_ADCGAINGN4_RESET             0x00004000            /*      Reset Value for ADCGAINGN4  */
#define REG_AFE_ADCGAINGN4                   0x00002278            /*  AFE ADC Gain Calibration Auxiliary Input Channel (PGA Gain=4) */
#define REG_AFE_ADCPGAOFFSETCANCEL_RESET     0x00000000            /*      Reset Value for ADCPGAOFFSETCANCEL  */
#define REG_AFE_ADCPGAOFFSETCANCEL           0x00002280            /*  AFE ADC Offset Cancellation (Optional) */
#define REG_AFE_ADCGNHSTIA_RESET             0x00004000            /*      Reset Value for ADCGNHSTIA  */
#define REG_AFE_ADCGNHSTIA                   0x00002284            /*  AFE ADC Gain Calibration for HS TIA Channel */
#define REG_AFE_ADCOFFSETLPTIA0_RESET        0x00000000            /*      Reset Value for ADCOFFSETLPTIA0  */
#define REG_AFE_ADCOFFSETLPTIA0              0x00002288            /*  AFE ADC Offset Calibration ULP-TIA0 Channel */
#define REG_AFE_ADCGNLPTIA0_RESET            0x00004000            /*      Reset Value for ADCGNLPTIA0  */
#define REG_AFE_ADCGNLPTIA0                  0x0000228C            /*  AFE ADC GAIN Calibration for LP TIA0 Channel */
#define REG_AFE_ADCPGAGN4OFCAL_RESET         0x00004000            /*      Reset Value for ADCPGAGN4OFCAL  */
#define REG_AFE_ADCPGAGN4OFCAL               0x00002294            /*  AFE ADC Gain Calibration with DC Cancellation(PGA G=4) */
#define REG_AFE_ADCGAINGN9_RESET             0x00004000            /*      Reset Value for ADCGAINGN9  */
#define REG_AFE_ADCGAINGN9                   0x00002298            /*  AFE ADC Gain Calibration Auxiliary Input Channel (PGA Gain=9) */
#define REG_AFE_ADCOFFSETEMPSENS1_RESET      0x00000000            /*      Reset Value for ADCOFFSETEMPSENS1  */
#define REG_AFE_ADCOFFSETEMPSENS1            0x000022A8            /*  AFE ADC Offset Calibration  Temp Sensor Channel 1 */
#define REG_AFE_ADCGAINDIOTEMPSENS_RESET     0x00004000            /*      Reset Value for ADCGAINDIOTEMPSENS  */
#define REG_AFE_ADCGAINDIOTEMPSENS           0x000022AC            /*  AFE ADC Gain Calibration Diode Temperature Sensor Channel */
#define REG_AFE_DACOFFSETATTENHP_RESET       0x00000000            /*      Reset Value for DACOFFSETATTENHP  */
#define REG_AFE_DACOFFSETATTENHP             0x000022B8            /*  AFE DAC Offset with Attenuator Enabled (HP Mode) */
#define REG_AFE_DACOFFSETHP_RESET            0x00000000            /*      Reset Value for DACOFFSETHP  */
#define REG_AFE_DACOFFSETHP                  0x000022BC            /*  AFE DAC Offset with Attenuator Disabled (HP Mode) */
#define REG_AFE_ADCGNLPTIA1_RESET            0x00004000            /*      Reset Value for ADCGNLPTIA1  */
#define REG_AFE_ADCOFFSETLPTIA1              0x000022C0            /*  AFE ADC Offset Calibration ULP-TIA0 Channel */
#define REG_AFE_ADCGNLPTIA1                  0x000022C4            /*  AFE ADC GAIN Calibration for LP TIA1 Channel */
#define REG_AFE_ADCOFFSETGN2_RESET           0x00000000            /*      Reset Value for ADCOFFSETGN2  */
#define REG_AFE_ADCOFFSETGN2                 0x000022C8            /*  AFE Offset Calibration Auxiliary Channel (PGA Gain =2) */
#define REG_AFE_ADCOFFSETGN1P5_RESET         0x00000000            /*      Reset Value for ADCOFFSETGN1P5  */
#define REG_AFE_ADCOFFSETGN1P5               0x000022CC            /*  AFE Offset Calibration Auxiliary Channel (PGA Gain =1.5) */
#define REG_AFE_ADCOFFSETGN9_RESET           0x00000000            /*      Reset Value for ADCOFFSETGN9  */
#define REG_AFE_ADCOFFSETGN9                 0x000022D0            /*  AFE Offset Calibration Auxiliary Channel (PGA Gain =9) */
#define REG_AFE_ADCOFFSETGN4_RESET           0x00000000            /*      Reset Value for ADCOFFSETGN4  */
#define REG_AFE_ADCOFFSETGN4                 0x000022D4            /*  AFE Offset Calibration Auxiliary Channel (PGA Gain =4) */
#define REG_AFE_PMBW_RESET                   0x00088800            /*      Reset Value for PMBW  */
#define REG_AFE_PMBW                         0x000022F0            /*  AFE Power Mode Configuration */
#define REG_AFE_SWMUX_RESET                  0x00000000            /*      Reset Value for SWMUX  */
#define REG_AFE_SWMUX                        0x0000235C            /*  AFE Switch Mux for ECG */
#define REG_AFE_AFE_TEMPSEN_DIO_RESET        0x00020000            /*      Reset Value for AFE_TEMPSEN_DIO  */
#define REG_AFE_AFE_TEMPSEN_DIO              0x00002374            /*  AFE AFE_TEMPSEN_DIO */
#define REG_AFE_ADCBUFCON_RESET              0x005F3D00            /*      Reset Value for ADCBUFCON  */
#define REG_AFE_ADCBUFCON                    0x0000238C            /*  AFE Configure ADC Input Buffer */
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
